RamiroMadera/Proyecto_GENERATOR/firmware_v3/documentation/CIAA_Boards/NXP_LPC54102/Pico-CIAA/Guia_picoCIAAv1.0_rfz.pdf

# picoCIAA v1.0

### Especificaciones técnicas y detalle de conectores

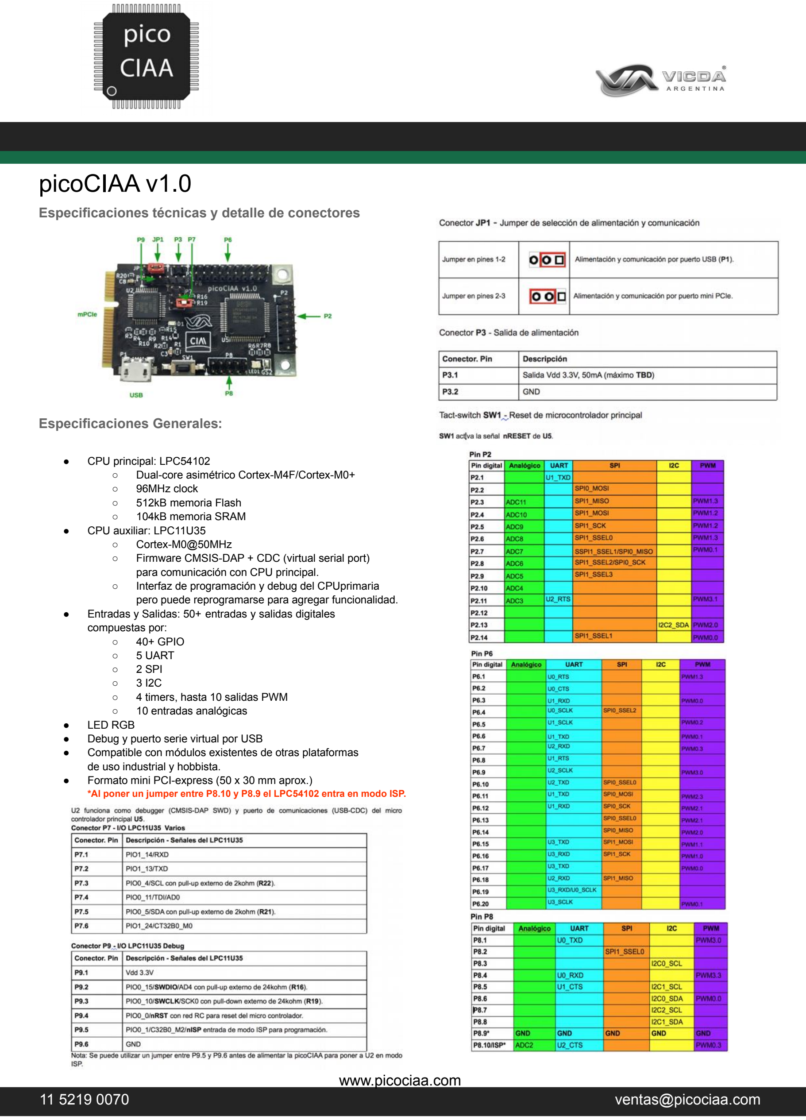
[picture p9: page 1]

### Especificaciones Generales:

- CPU principal: LPC54102
- Dual-core asimétrico Cortex-M4F/Cortex-M0+
- 96MHz clock
- 512kB memoria Flash
- 104kB memoria SRAM
- CPU auxiliar: LPC11U35
- Cortex-M0@50MHz
- Firmware CMSIS-DAP + CDC (virtual serial port) para comunicación con CPU principal.
- Interfaz de programación y debug del CPUprimaria pero puede reprogramarse para agregar funcionalidad.
- Entradas y Salidas: 50+ entradas y salidas digitales compuestas por:
- 40+ GPIO
- 5 UART
- 2 SPI
- 3 I2C
- 4 timers, hasta 10 salidas PWM
- 10 entradas analógicas
- LED RGB
- Debug y puerto serie virtual por USB
- Compatible con módulos existentes de otras plataformas
de uso industrial y hobbista.
- Formato mini PCI-express (50 x 30 mm aprox.)
*Al poner un jumper entre P8.10 y P8.9 el LPC54102 entra en modo ISP.

## www.picociaa.com

11 5219 0070 | ventas@picociaa.com
