RamiroMadera/Proyecto_GENERATOR/firmware_v3/examples/c/sapi/bluetooth/MIT App Inventor 2.pdf

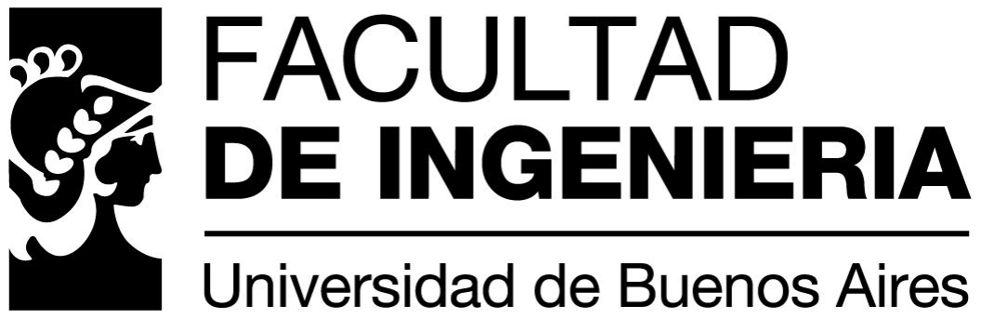
[picture p13: figure]

## Carrera de Especialización en Sistemas Embebidos (CESE) de la FI-UBA

### 8. Protocolos de comunicación en Sistemas Embebidos

MIT App Inventor 2

Profesores:
- Esp. Ing. Eric Pernia.
- Dr. Ing. Pablo Gómez.

“MIT App Inventor 2”
por Esp. Lic. Agustin Bassi, se distribuye bajo una Licencia Creative Commons Atribución-CompartirIgual 4.0 Internacional.

## Licencia

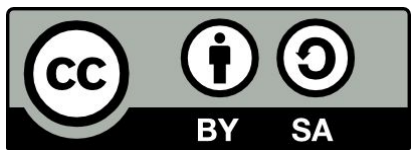
[picture p14: figure]

Para realizar una aplicación en Android para probar la comunicación con la EDU-CIAA-NXP vamos a utilizar APP Inventor, que es una herramienta sencilla para desarrollar aplicaciones Android evitando utilizar las herramientas típicas las cuales consisten en lenguaje de programación Java, XML, emulación virtual y el entorno de desarrollo Android Studio. (https://developer.android.com/studio/)

APP Inventor es un desarrollo de Google que permite programar aplicaciones para Android mediante programación gráfica. Posteriormente, el proyecto fue retomado por el MIT y ahora es conocido como MIT App Inventor 2.

MIT App Inventor 2 es una herramienta para desarrollo on line por lo que requiere conexión permanente a Internet.

## Introducción

Paso 1

Tener una cuenta en Gmail
En https://accounts.google.com/ se puede crear una cuenta. Si ya se tiene cuenta, este paso es innecesario.

Paso 2

Ir a la página de MIT App Inventor 2
Dirigirse a http://appinventor.mit.edu/explore/front.html Allí inicia todo!

## Configuración APP Inventor 2

Paso 3 - Iniciar MIT App Inventor

Dirigirse a http://appinventor.mit.edu/explore/index-2.html y dar clic en “Create Apps”.

## Configuración APP Inventor 2

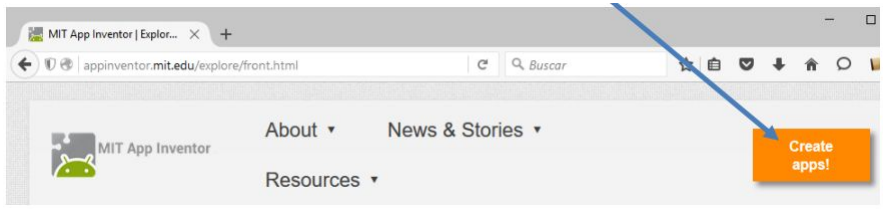
[picture p15: figure]

Paso 4 - Acceder a APP Inventor 2 con la cuenta de Google.

## Configuración APP Inventor 2

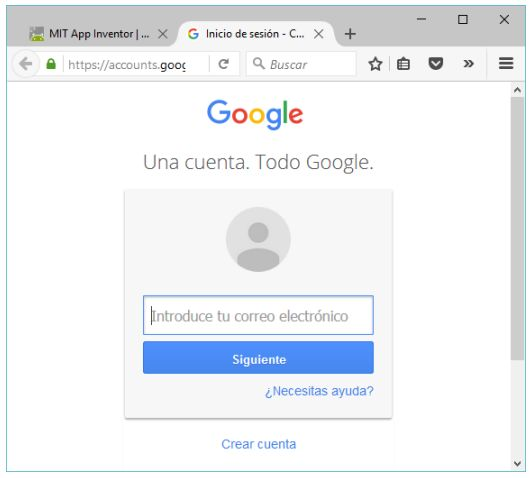
[picture p16: figure]

Paso 5 - Pantalla de inicio APP Inventor.

Al ser la primera vez, no se tienen proyectos en la cuenta.

## Configuración APP Inventor 2

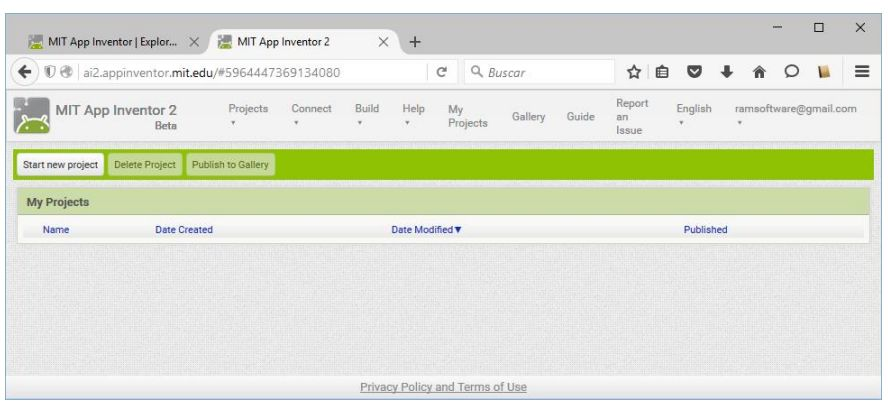
[picture p17: figure]

Paso 6 - Cambiar idioma en APP Inventor

Si es de preferencia, cambiar el idioma a Español.

## Configuración APP Inventor 2

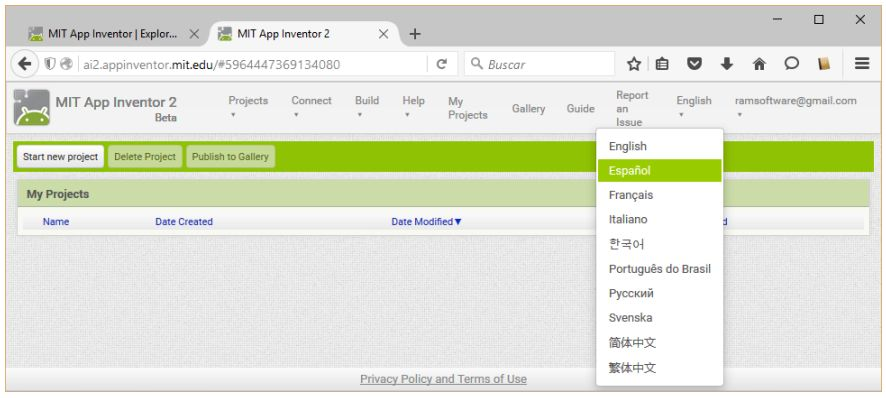
[picture p18: figure]

Paso 7 - Aceptar la información.
Tildar la opción “Do not show Again” para que no vuelva a aparecer este cartel nuevamente.

## Configuración APP Inventor 2

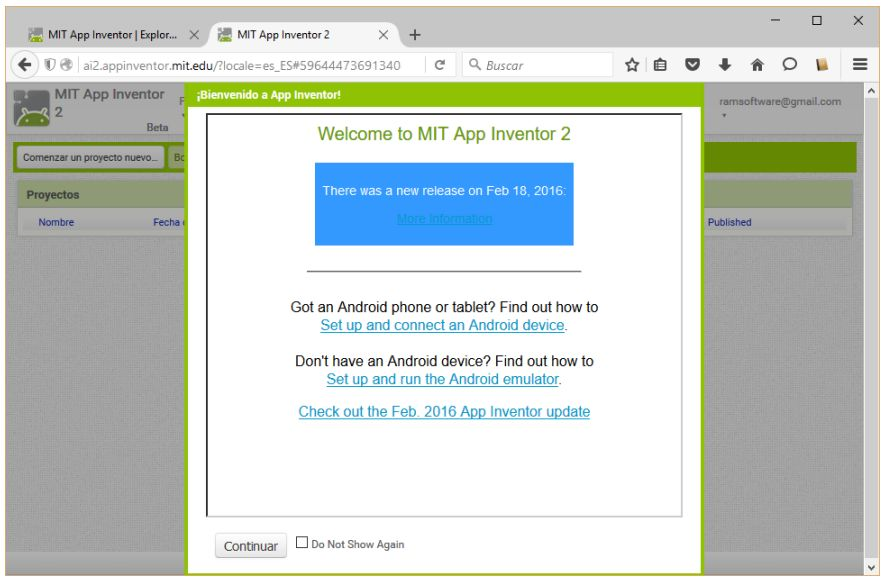
[picture p19: figure]

Paso 8 - Fin de la configuración

Bienvenido a APP Inventor 2 !!!

## Configuración APP Inventor 2

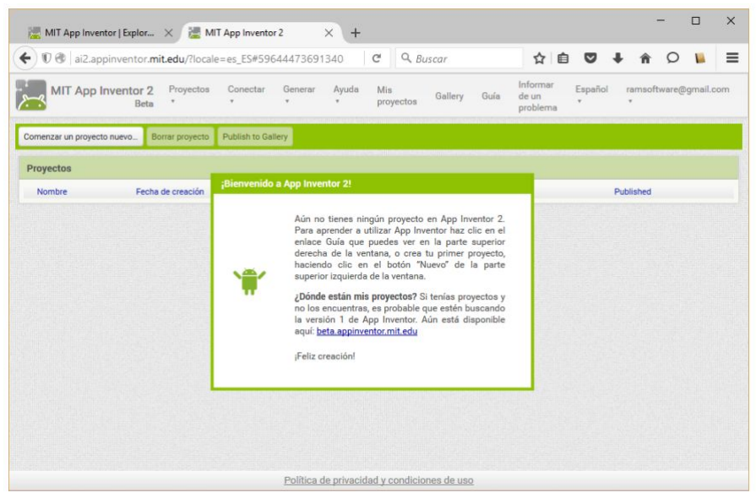
[picture p20: figure]

APP Inventor 2 permite debuggear la aplicación creada directamente en el celular.

Para que esto sea posible es necesario instalar una aplicación de APP Inventor 2 que se encuentra en el Play Store de Google.

Descargar la aplicación y dar los permisos necesarios para que pueda ejecutarse.

## Instalar aplicación APP Inventor 2

## Instalar aplicación APP Inventor 2

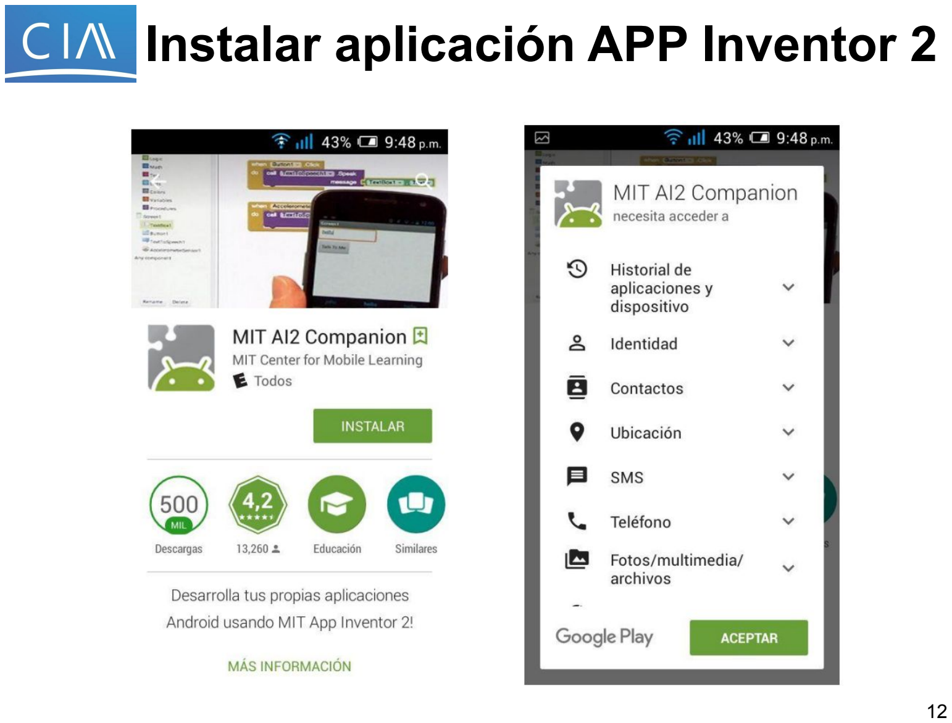
[picture p21: page 12]

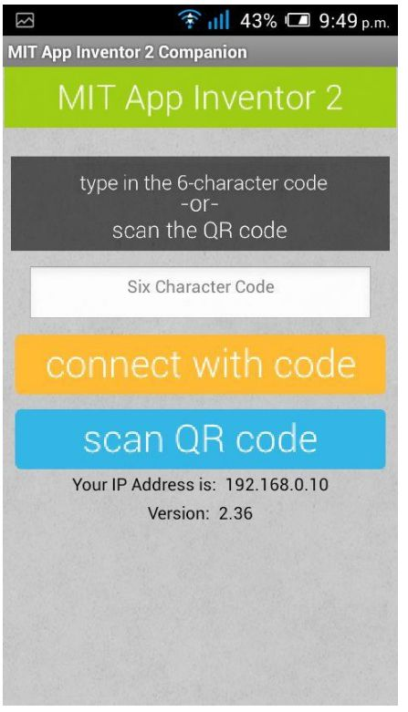
[picture p22: figure]

La aplicación MIT App
Inventor 2 Companion va a
permitir vincular el
desarrollo realizado dentro de la web con el
smartphone personal.

Mediante el escaneo de un
código QR o la escritura del código provisto en la web, automáticamente se carga
la aplicación desarrollada en el smartphone.

## Instalar aplicación APP Inventor 2

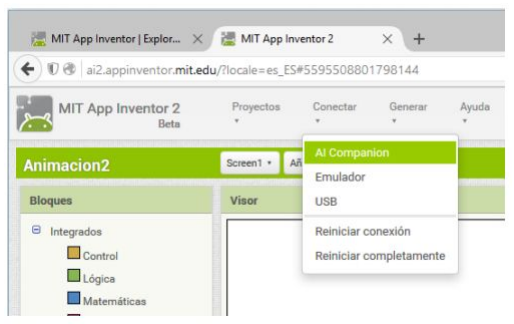
[picture p23: figure]

Dentro de la web de App
Inventor 2, seleccionar
“Conectar” y luego “AI
Companion”.

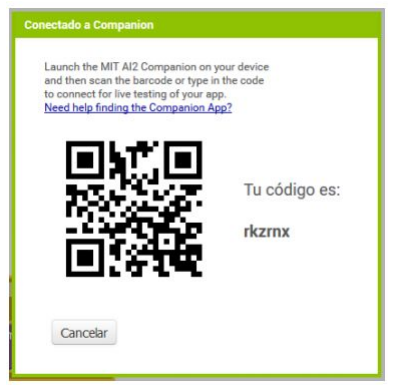
[picture p24: figure]

Esto genera el código QR
que debe ser escaneado
desde la aplicación de APP Inventor previamente
instalada en el smartphone.

## Instalar aplicación APP Inventor 2

# ¿Preguntas?

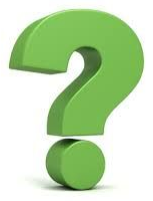
[picture p25: figure]

## Consultas:

ericpernia@gmail.com
elpablogomez@gmail.com
sergiordj@gmail.com

# ¡Muchas gracias!

- http://www.bolanosdj.com.ar/MOVIL/LENGUAJES/Usan

do-MIT-App-Inventor-2.pdf (http://www.bolanosdj.com.ar/MOVIL/LENGUAJES/Usando-MIT-App-Inventor-2.pdf)

- http://ai2.appinventor.mit.edu/

## Bibliografía
