RamiroMadera/Proyecto_GENERATOR/firmware_v3/examples/c/sapi/bluetooth/hc05_uart_bridge/APP Inventor - Hola Mundo con HC05 o HC06.pdf

# Carrera de Especialización en Sistemas Embebidos (CESE) de la FI-UBA

## 8. Protocolos de comunicación en Sistemas Embebidos

## APP Inventor - Hola Mundo con HC05 o HC06

Profesores:
- Esp. Ing. Eric Pernia.
- Dr. Ing. Pablo Gómez.

## “APP Inventor - Hola Mundo!” por Esp. Lic. Agustin Bassi, se distribuye bajo una Licencia Creative Commons Atribución-CompartirIgual 4.0

Internacional.

# Licencia


## El objetivo será crear una aplicación Android que tenga comunicación con la EDU-CIAA-NXP mediante el módulo

Bluetooth HC05 o HM10.

Los materiales necesarios serán.

- EDU-CIAA-NXP.
- Módulo HC05 o HM10.
- Cables de conexión entre EDU CIAA y HC05.
- Cuenta creada en APP Inventor.
- Smartphone con Android.

# Introducción

# Cargar programa en EDU CIAA

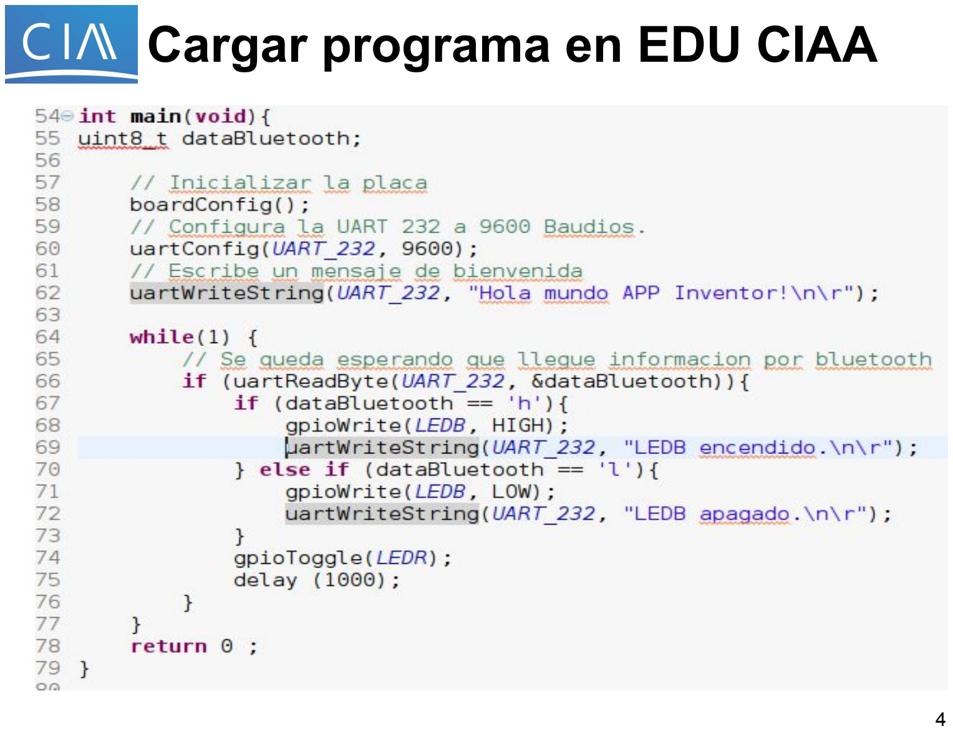
[picture p26: page 4]

## Comenzar creando un proyecto nuevo con el botón “Comenzar

nuevo proyecto”.

Ingresar como nombre Estación Metereológica.

# Hola Mundo App Inventor 2!

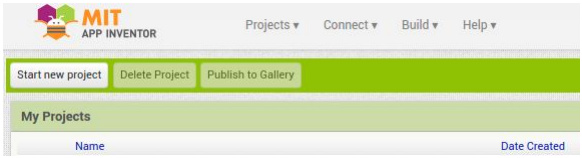
[picture p27: figure]

Al iniciar el proyecto, se verá una ventana como esta.

# Hola Mundo App Inventor 2!

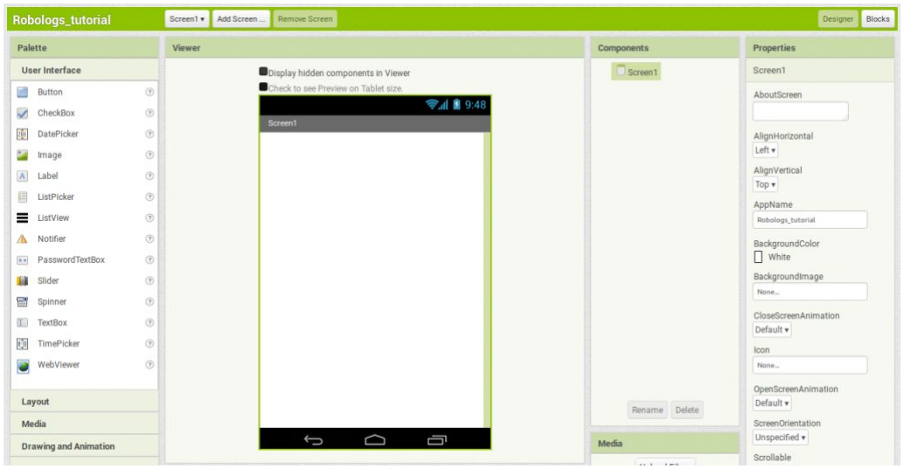
[picture p28: figure]

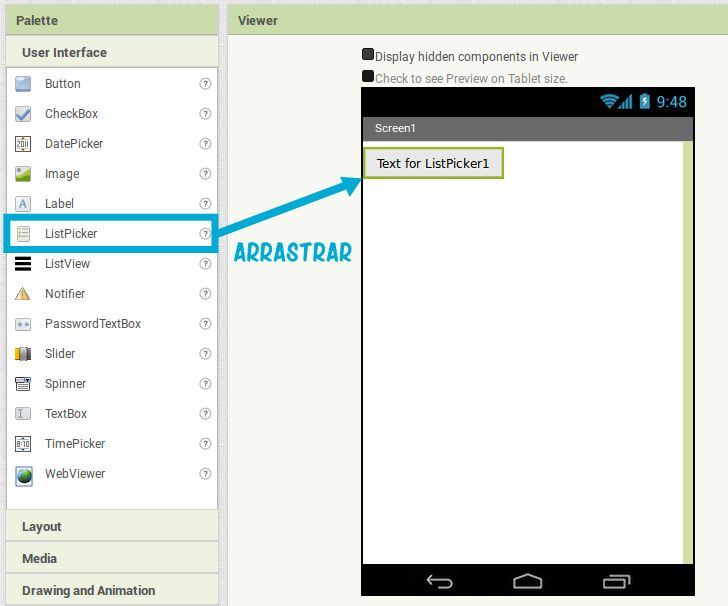
[picture p29: figure]

Empezar yendo a

Palette y buscar el

elemento List Picker.

Se trata de menú

desplegable, que se

programa para que

muestre los

dispositivos Bluetooth

cercanos y se conecte

a uno. Arrastrarlo

hasta la pantalla.

# Hola Mundo App Inventor 2!

A la derecha, en el menú Properties, cambiar el texto

del List Picker. Escribir “Dispositivos”.

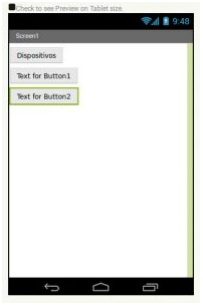
[picture p30: figure]

Volver al menú Palette y añadir dos elementos de tipo

Button a la aplicación, de la misma forma que se

colocó el List Picker.

Seleccionar cada uno de los botones y cambiarles el

nombre. A uno llamar “Encender LED” y al otro

“Apagar LED”. Con un botón se encenderá el LEDB y

con el otro se apagará.

# Hola Mundo App Inventor 2!

La comunicación entre la APP y el sistema embebido debe ser

bidireccional. Se deben agregar los objetos destinados a la

recepción de datos.

Agregar desde el menú | Palette->User Interface | un objeto del tipo

Label y en sus propiedades escribirle el texto “Información

Recibida”.

Como último objeto visual, debajo del Label agregar un TextBox.

# Hola Mundo App Inventor 2!

Lo que se ha añadido hasta ahora son componentes visibles. El usuario puede verlos e interactuar con ellos. Pero hay otro tipo de componentes, llamados non-visible components, que sirven para activar algunas funcionalidades como el Giroscopio, la antena WiFi o Bluetooth.

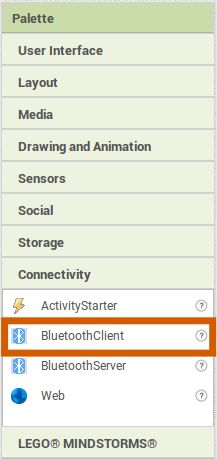
[picture p31: figure]

Para poder conectar con la CIAA se necesita que la aplicación pueda usar la antena Bluetooth.

Ir a Palette->Connectivity y arrastrar Bluetooth Client a la pantalla.

# Hola Mundo App Inventor 2!

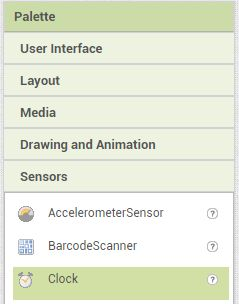
[picture p32: figure]

El último objeto necesario a agregar es

un timer que chequee si hay información

disponible proveniente del sistema

embebido.

Esto se realiza desde | Palette->Sensors
y arrastrando un objeto | Clock.

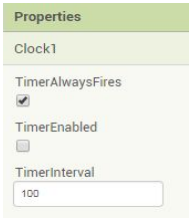
[picture p33: figure]

En las propiedades del clock setear que

se dispare cada 100 ms y que arranque

deshabilitado.

# Hola Mundo App Inventor 2!

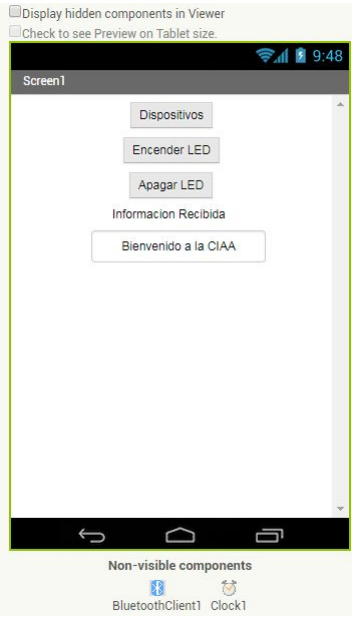
[picture p34: figure]

A esta altura, la aplicación debería lucir como en la imagen.

Hasta aquí el diseño. Es hora de configurar cada uno de los componentes.

Arriba a la derecha hay dos botones juntos: Design y Blocks. El primero abre la ventana de diseño, que permite colocar todos los
componentes de la aplicación. Blocks abre una ventana para programar los bloques.

# Hola Mundo App Inventor 2!

Lo primero es programar el menú desplegable. A la derecha, seleccionar ListPicker1 y se abrirá un menú en el que aparecen los bloques relacionados con este objeto.
Hay que programar en el desplegable dos cosas: qué debe hacer ANTES de seleccionar una opción del menú desplegable y DESPUÉS de seleccionar una.

Antes de seleccionar una opción,

inicializar una lista con los nombres

de todos los dispositivos Bluetooth

que hay cerca.

Si el móvil tiene la comunicación

Bluetooth activada, ListPicker1

deberá establecer los nombres de

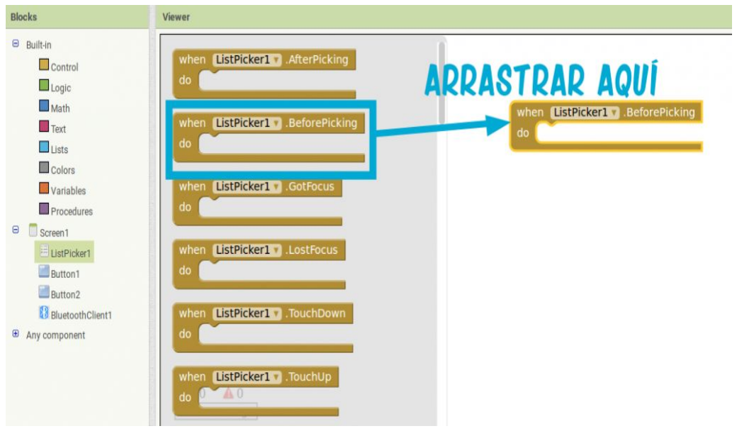
[picture p35: figure]

los dispositivos cercanos como elementos de la lista.

Dentro del menú de bloques de | ListPicker1 arrastrar. BeforePicking | al espacio
en blanco.

# Hola Mundo App Inventor 2!

# Hola Mundo App Inventor 2!

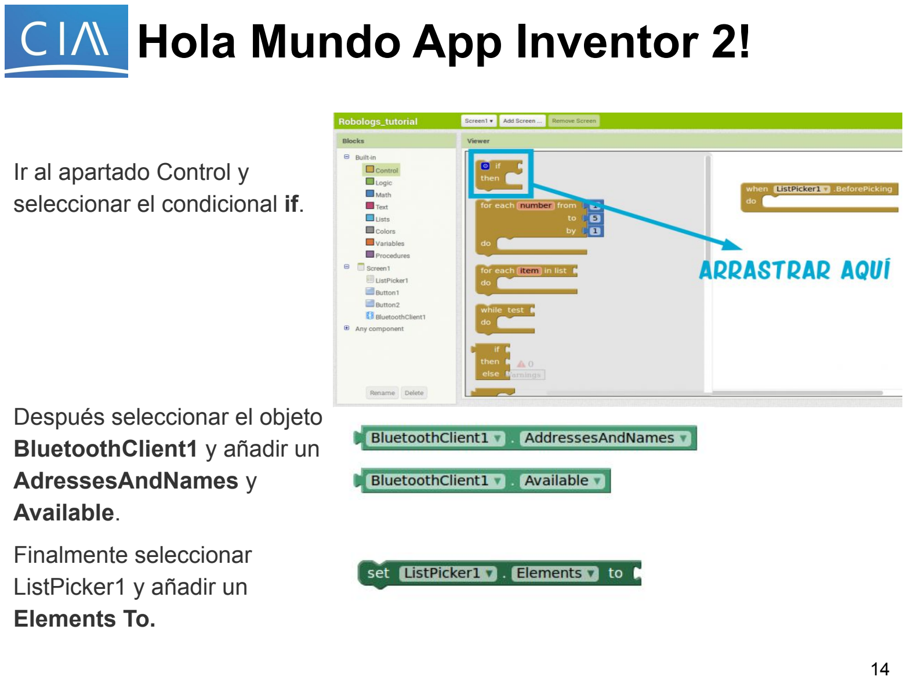
[picture p36: page 14]

Ir al apartado Control y
seleccionar el condicional if.

Después seleccionar el objeto
BluetoothClient1 | y añadir un
AdressesAndNames | y
Available.

Finalmente seleccionar
ListPicker1 y añadir un
Elements To.

# Hola Mundo App Inventor 2!

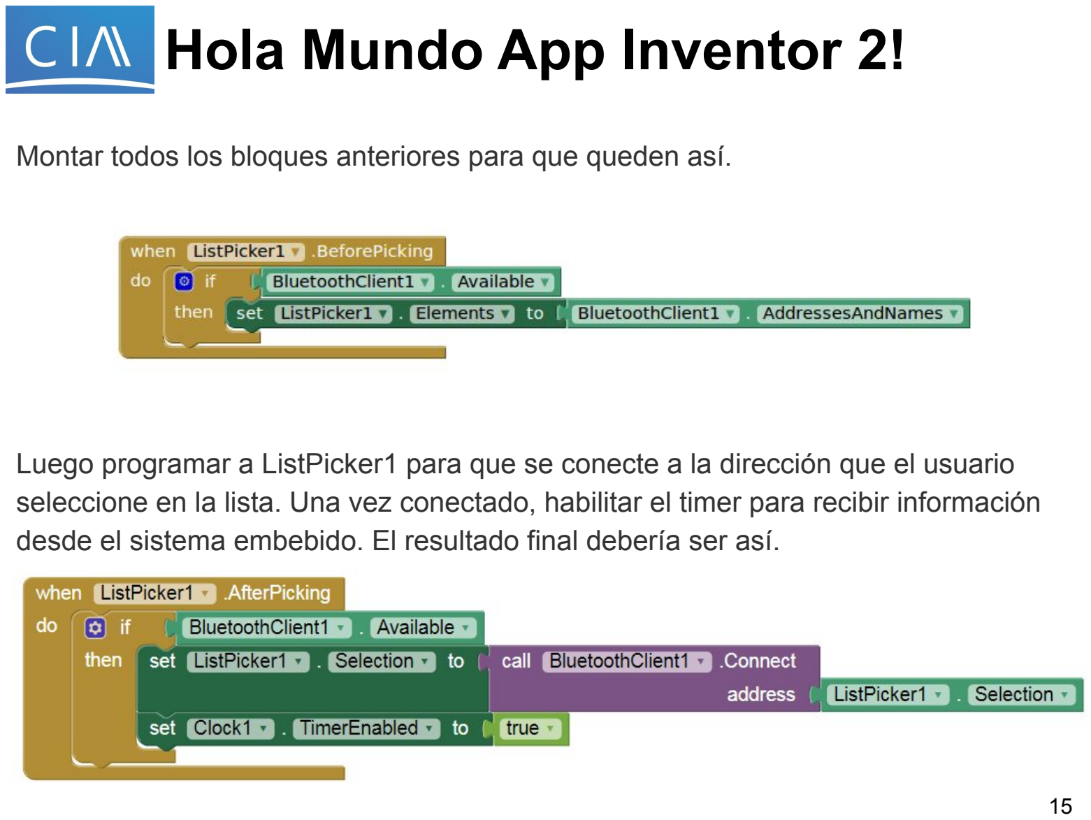
[picture p37: page 15]

Montar todos los bloques anteriores para que queden así.

Luego programar a ListPicker1 para que se conecte a la dirección que el usuario seleccione en la lista. Una vez conectado, habilitar el timer para recibir información desde el sistema embebido. El resultado final debería ser así.

Al inicio de la aplicación deshabilitar el campo de texto donde se va a mostrar la info recibida así no se puede escribir en ese campo.

Si la aplicación recibe un dato enviado desde el sistema embebido lo debe mostrar en el campo de texto. Para chequear si la aplicación recibió datos, es necesario chequear periódicamente mediante el timer si hay datos disponibles en el objeto de conexión BluetoothClient1

# Hola Mundo App Inventor 2!

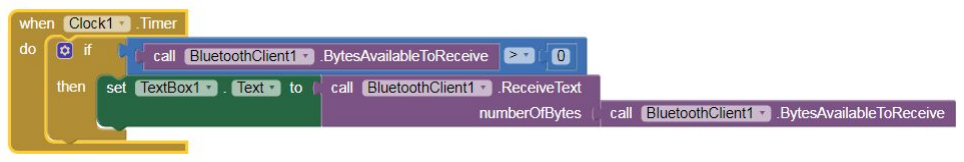
[picture p38: figure]

Finalmente configurar Button1 y Button2 para que al pulsarlos se envíe un texto a la dirección Bluetooth conectado.

# Hola Mundo App Inventor 2!

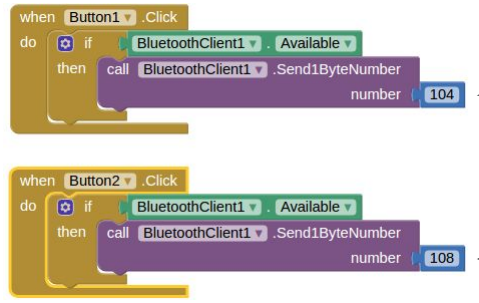
[picture p39: figure]

Corresponde al
ASCII ‘h’

Corresponde al
ASCII ‘l’

# Hola Mundo App Inventor 2!

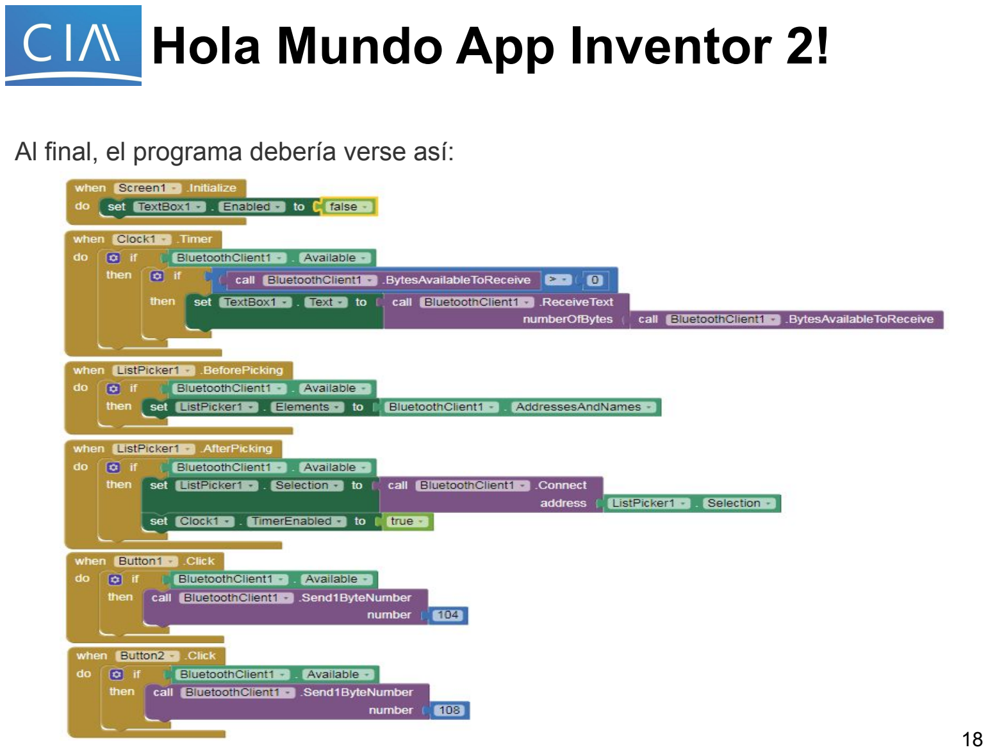
[picture p40: page 18]

Al final, el programa debería verse así:

# Hola Mundo App Inventor 2!

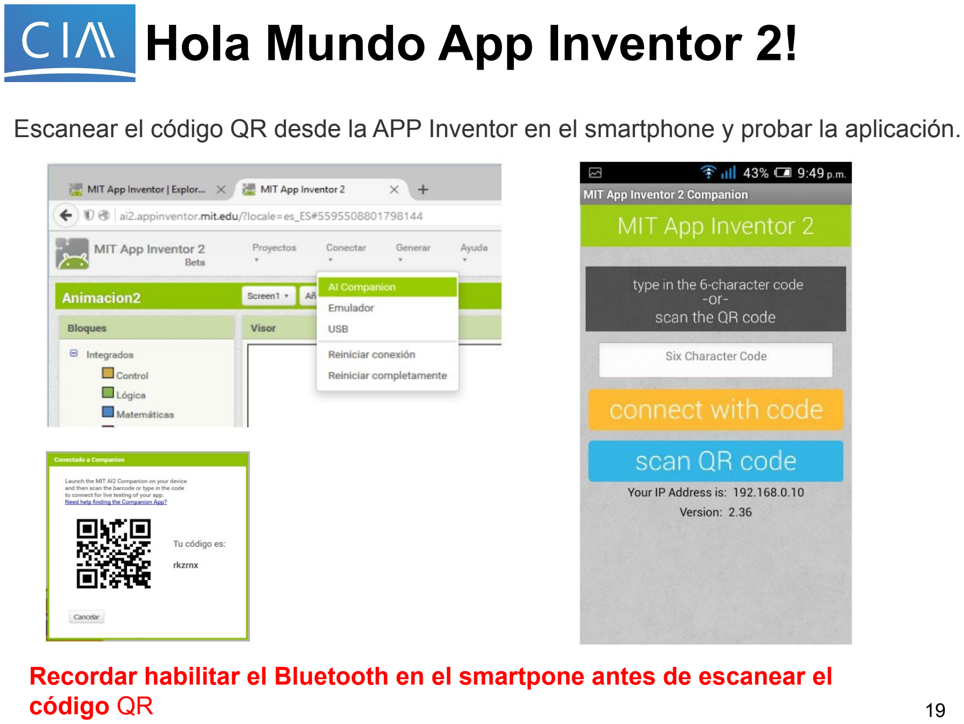
[picture p41: page 19]

Escanear el código QR desde la APP Inventor en el smartphone y probar la aplicación.

Recordar habilitar el Bluetooth en el smartpone antes de escanear el código QR

# ¿Preguntas?


# Consultas:

## ericpernia@gmail.com elpablogomez@gmail.com sergiordj@gmail.com

# ¡Muchas gracias!

## - http://ai2.appinventor.mit.edu/

## - http://www.bolanosdj.com.ar/MOVIL/LENGUAJES/Usan

do-MIT-App-Inventor-2.pdf (http://www.bolanosdj.com.ar/MOVIL/LENGUAJES/Usando-MIT-App-Inventor-2.pdf)

## - http://codeweek.eu/resources/spain/guia-iniciacion-app-

## inventor.pdf (http://codeweek.eu/resources/spain/guia-iniciacion-app-inventor.pdf)

## - https://robologs.net/2015/10/29/tutorial-de-arduino-bluet

ooth-y-android-2-crear-una-app-con-mit-inventor/ (https://robologs.net/2015/10/29/tutorial-de-arduino-bluetooth-y-android-2-crear-una-app-con-mit-inventor/)

# Bibliografía
