RamiroMadera/Proyecto_GENERATOR/firmware_v3/documentation/firmware/eclipse/Eclipse-Win01.png

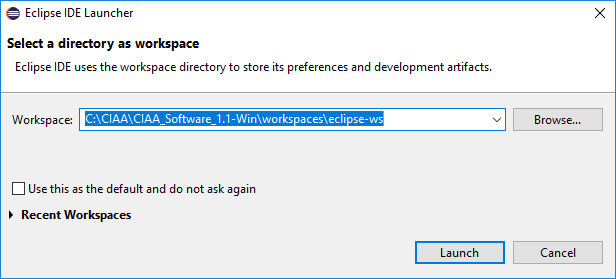
firmware_v3/documentation/firmware/eclipse/Eclipse-Win01.png
