RamiroMadera/Proyecto_GENERATOR/firmware_v3/documentation/firmware/eclipse/Eclipse-Win08.png

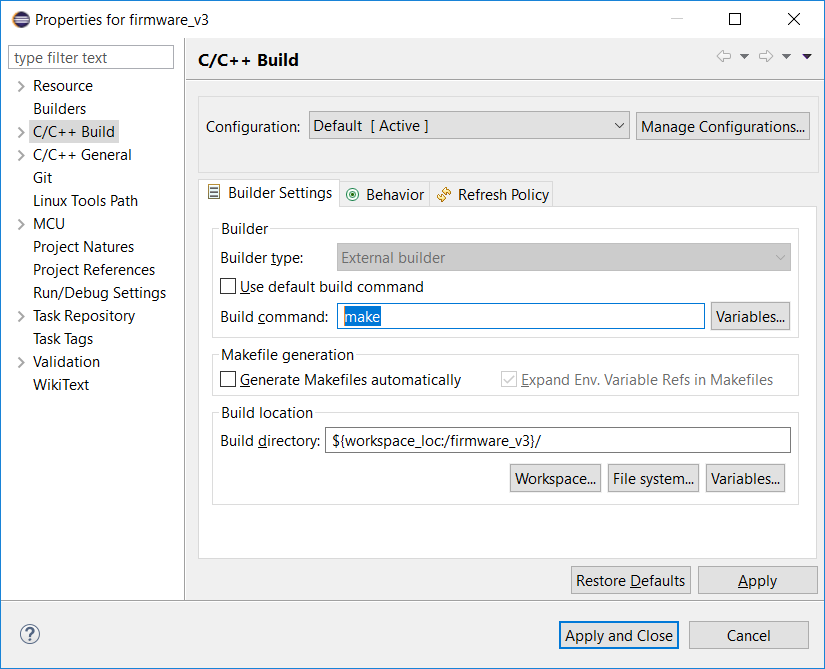
firmware_v3/documentation/firmware/eclipse/Eclipse-Win08.png
