RamiroMadera/Proyecto_GENERATOR/firmware_v3/documentation/firmware/eclipse/targets-03.png

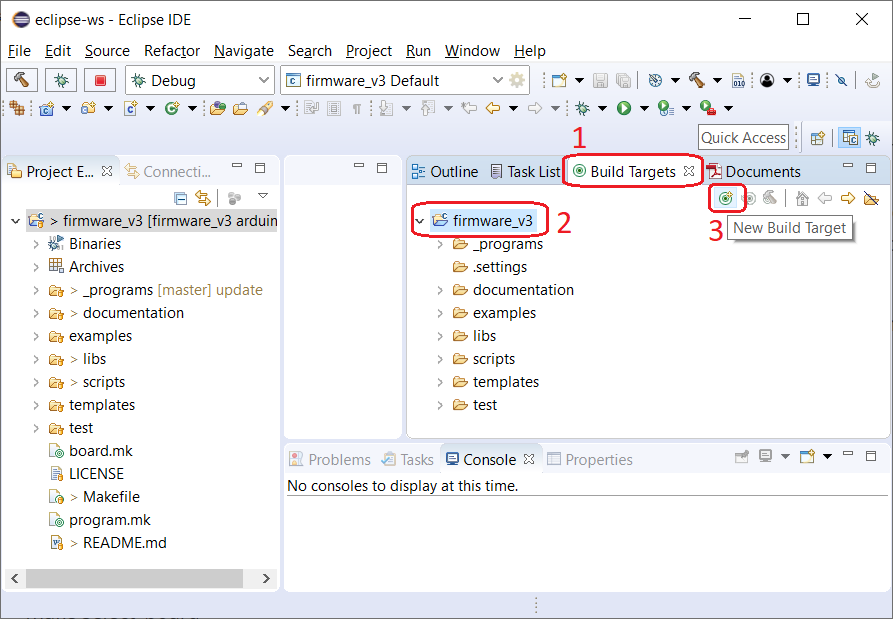
firmware_v3/documentation/firmware/eclipse/targets-03.png
