RamiroMadera/Proyecto_GENERATOR/firmware_v3/documentation/firmware/eclipse/targets-05.png

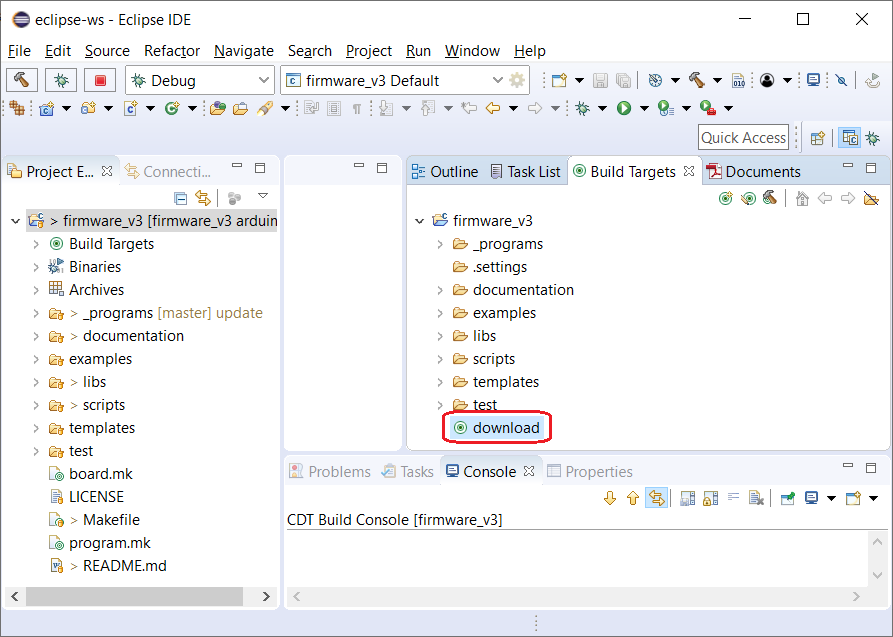
firmware_v3/documentation/firmware/eclipse/targets-05.png
