RamiroMadera/Proyecto_GENERATOR/firmware_v3/documentation/firmware/embedded_ide/open01.png

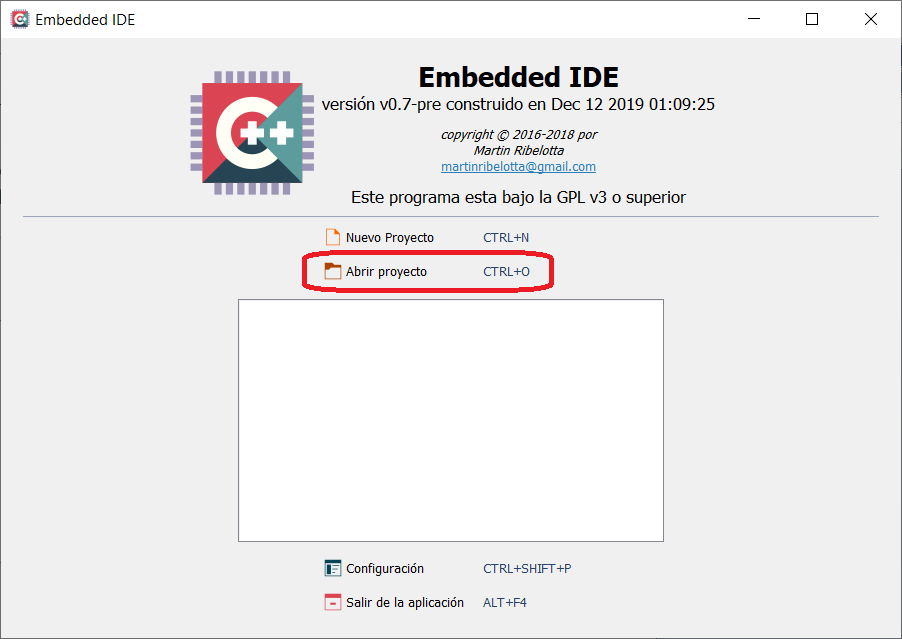
firmware_v3/documentation/firmware/embedded_ide/open01.png
