RamiroMadera/Proyecto_GENERATOR/firmware_v3/documentation/firmware/embedded_ide/open03.png

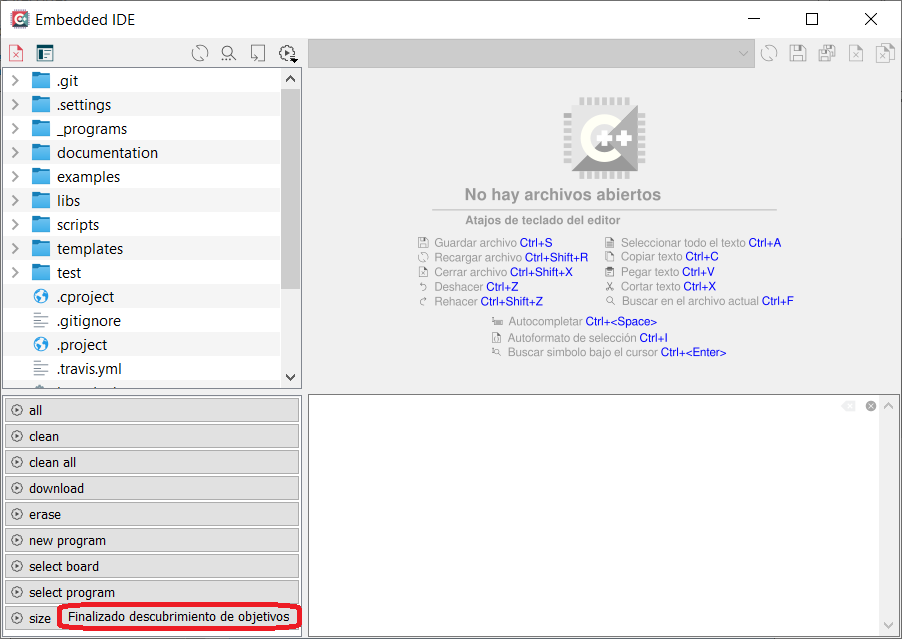
firmware_v3/documentation/firmware/embedded_ide/open03.png
