RamiroMadera/Proyecto_GENERATOR/firmware_v3/documentation/firmware/embedded_ide/targets.png

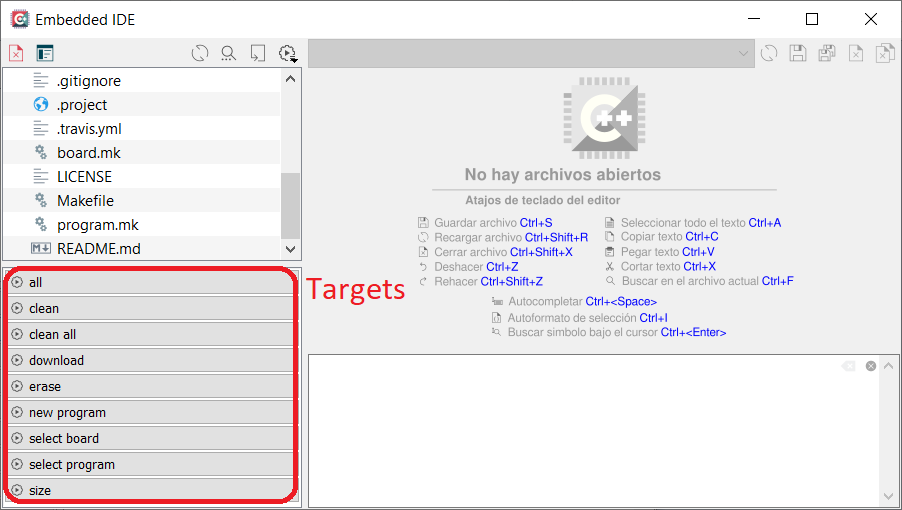
firmware_v3/documentation/firmware/embedded_ide/targets.png
