RamiroMadera/Proyecto_GENERATOR/firmware_v3/examples/c/lpc_open/timer_250ms_pulse/250msSignal.png

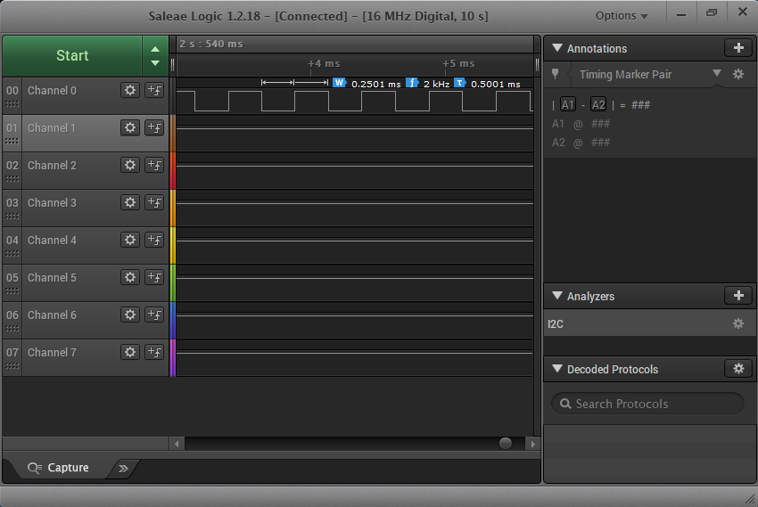
firmware_v3/examples/c/lpc_open/timer_250ms_pulse/250msSignal.png
