RamiroMadera/Proyecto_GENERATOR/firmware_v3/examples/c/sapi/adc_dac/adc_analog_stick_connection.png

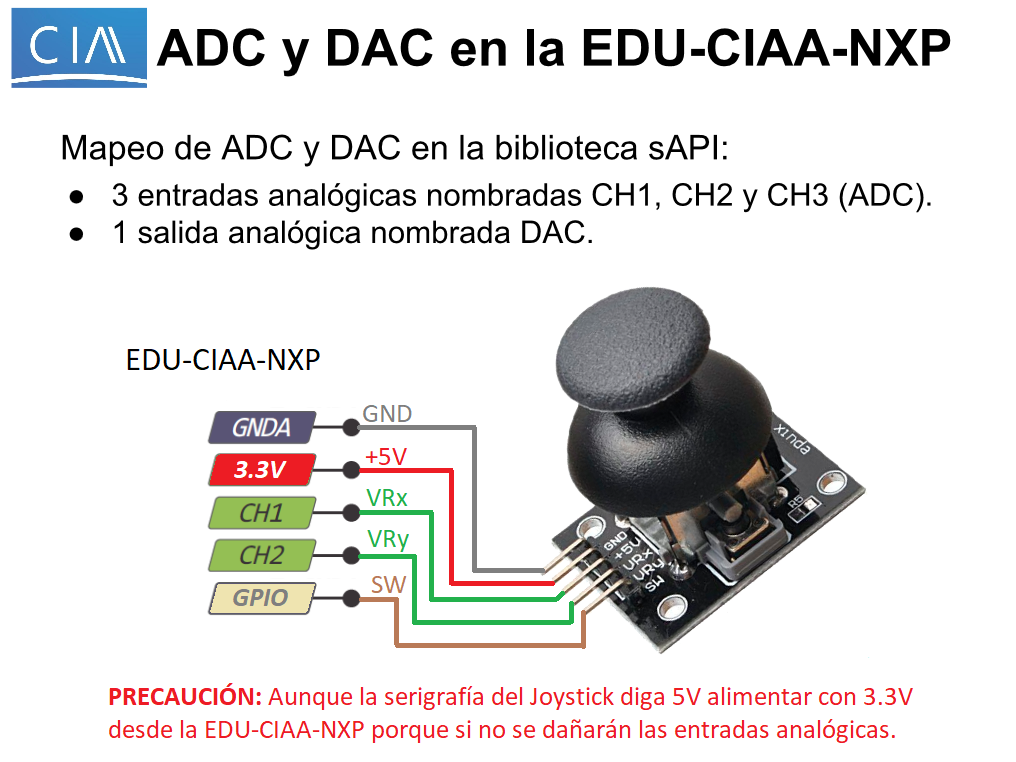
firmware_v3/examples/c/sapi/adc_dac/adc_analog_stick_connection.png
