RamiroMadera/Proyecto_GENERATOR/firmware_v3/examples/c/sapi/adc_dac/adc_dac_pins.png

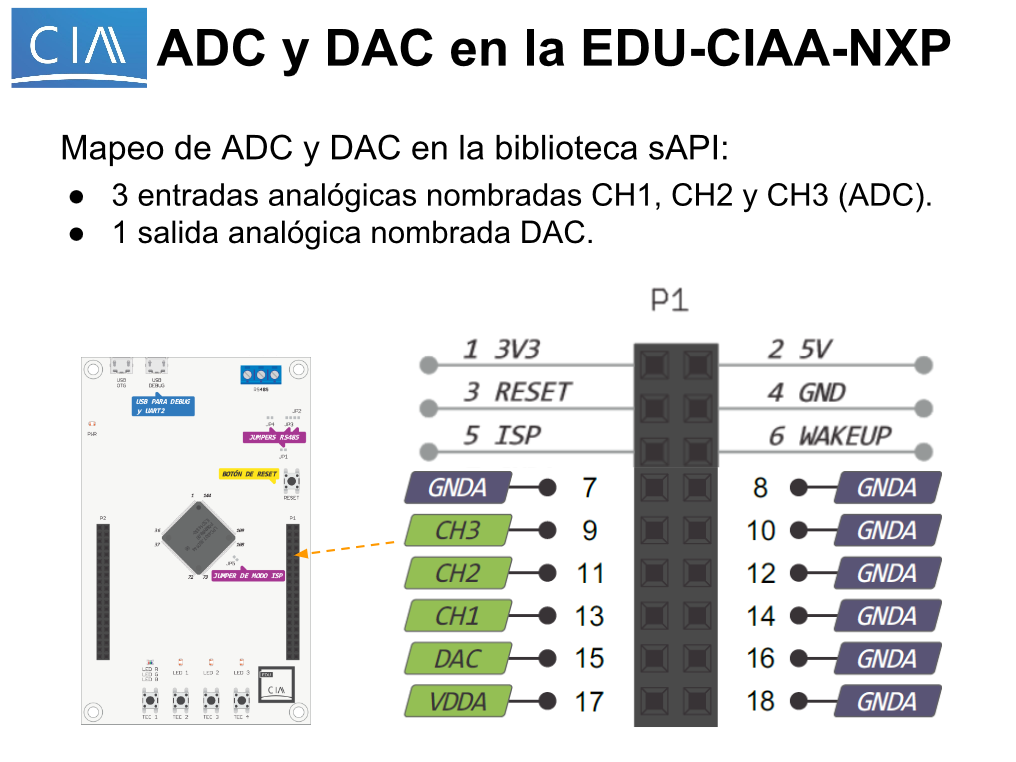
firmware_v3/examples/c/sapi/adc_dac/adc_dac_pins.png
