RamiroMadera/Proyecto_GENERATOR/firmware_v3/examples/c/sapi/bluetooth/hc05_uart_bridge/bluetooth_hc05_connection.png

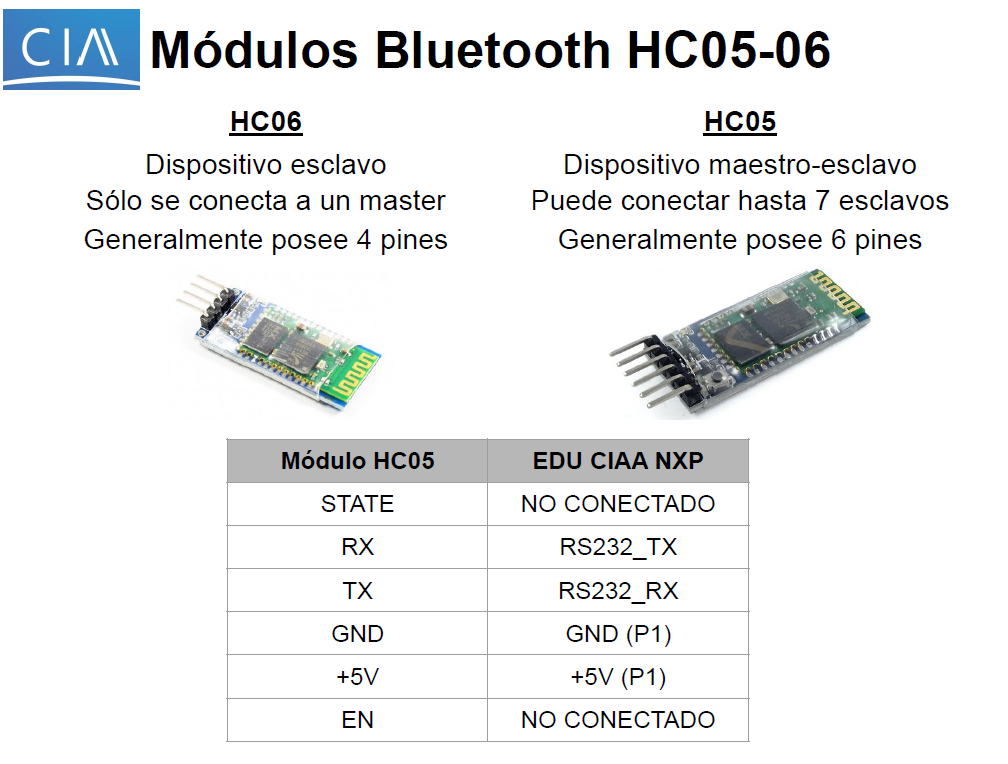
firmware_v3/examples/c/sapi/bluetooth/hc05_uart_bridge/bluetooth_hc05_connection.png
