RamiroMadera/Proyecto_GENERATOR/firmware_v3/examples/c/sapi/bluetooth/hm10_uart_bridge/bluetooth_ble_hm10_connection.png

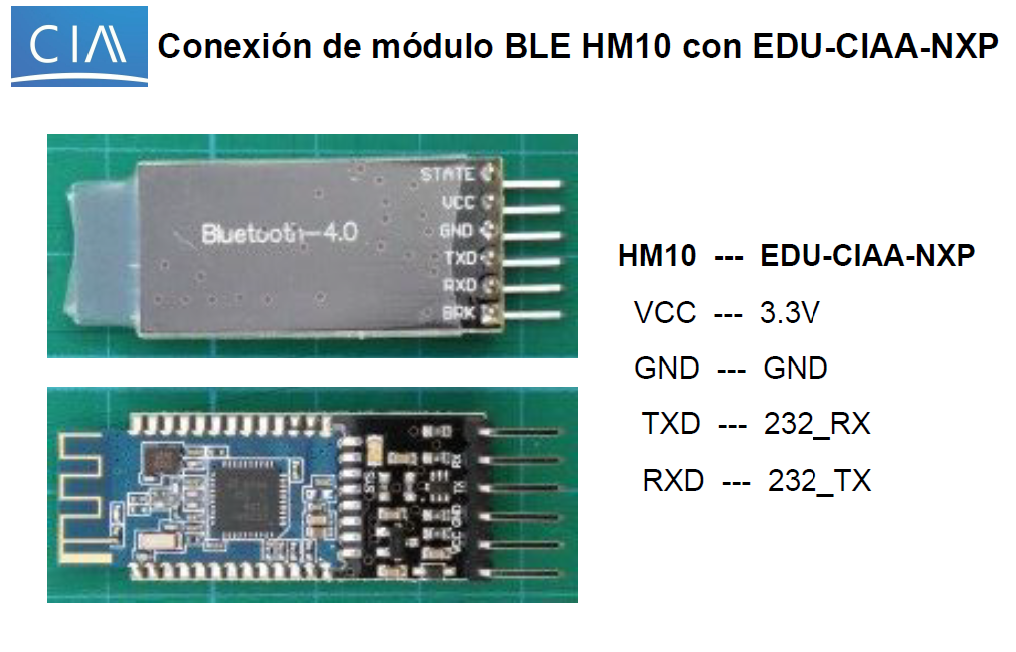
firmware_v3/examples/c/sapi/bluetooth/hm10_uart_bridge/bluetooth_ble_hm10_connection.png
