RamiroMadera/Proyecto_GENERATOR/firmware_v3/examples/c/sapi/dht11_temp_humidity/DHT11 Module and EDU-CIAA-NXP.png

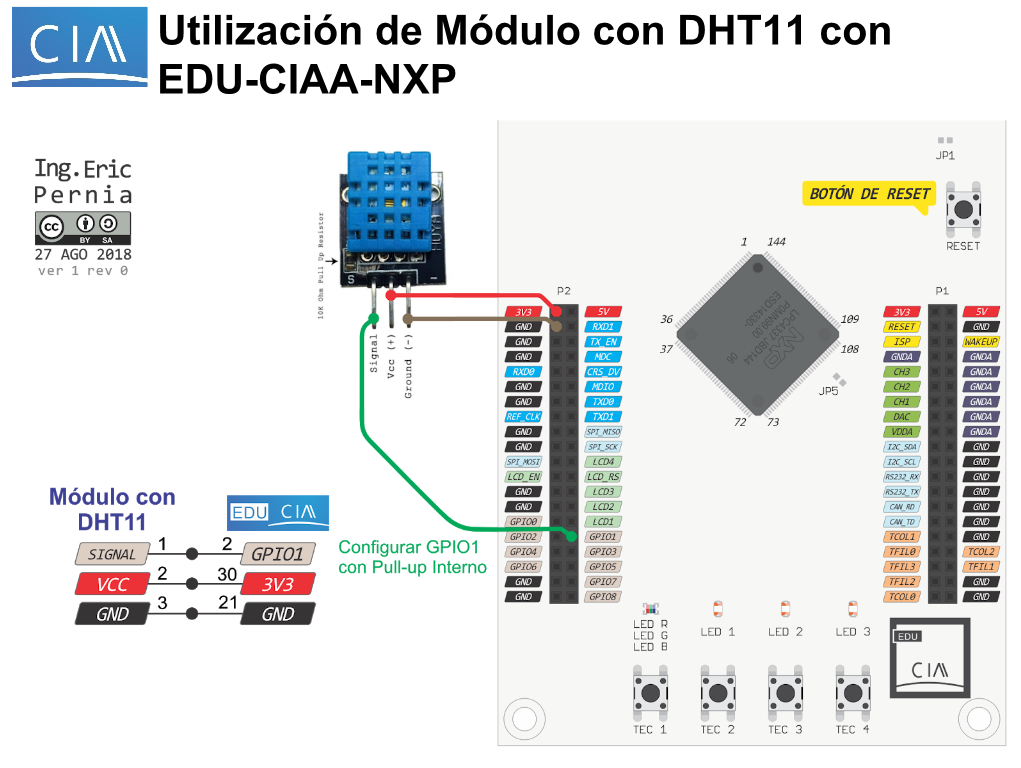
firmware_v3/examples/c/sapi/dht11_temp_humidity/DHT11 Module and EDU-CIAA-NXP.png
