RamiroMadera/Proyecto_GENERATOR/firmware_v3/examples/c/sapi/fatfs_sdcard_usbmsd/SD SPI.png

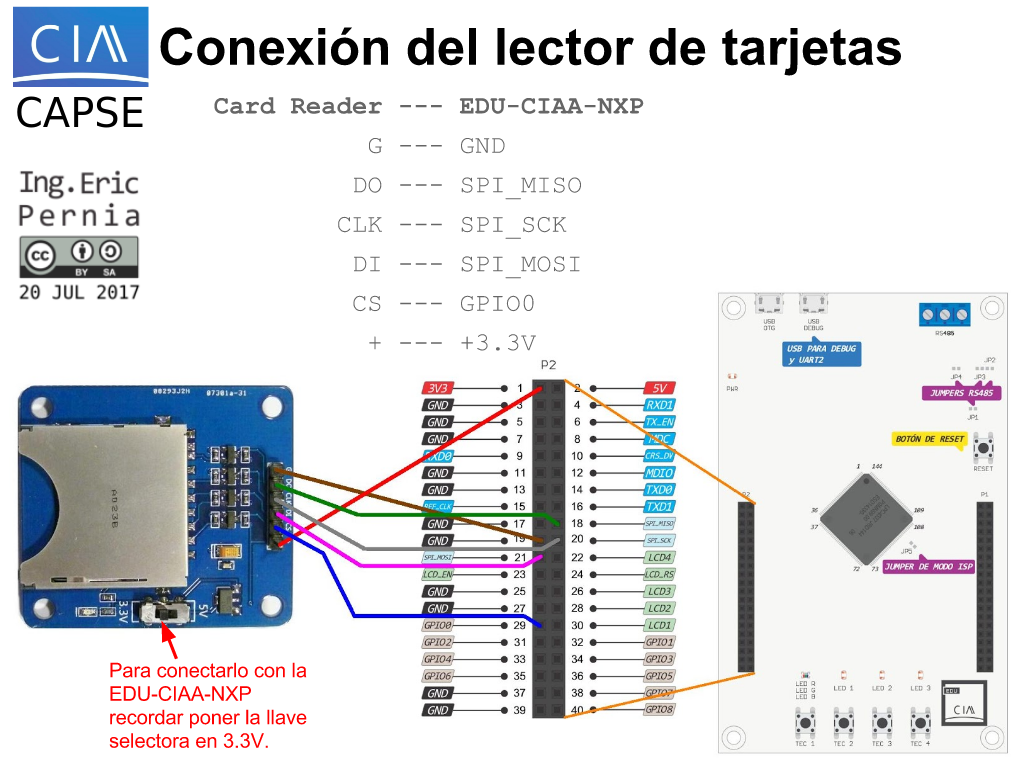
firmware_v3/examples/c/sapi/fatfs_sdcard_usbmsd/SD SPI.png
