RamiroMadera/Proyecto_GENERATOR/firmware_v3/examples/c/sapi/gpio/axis_interface/axis_pins_edu_ciaa.png

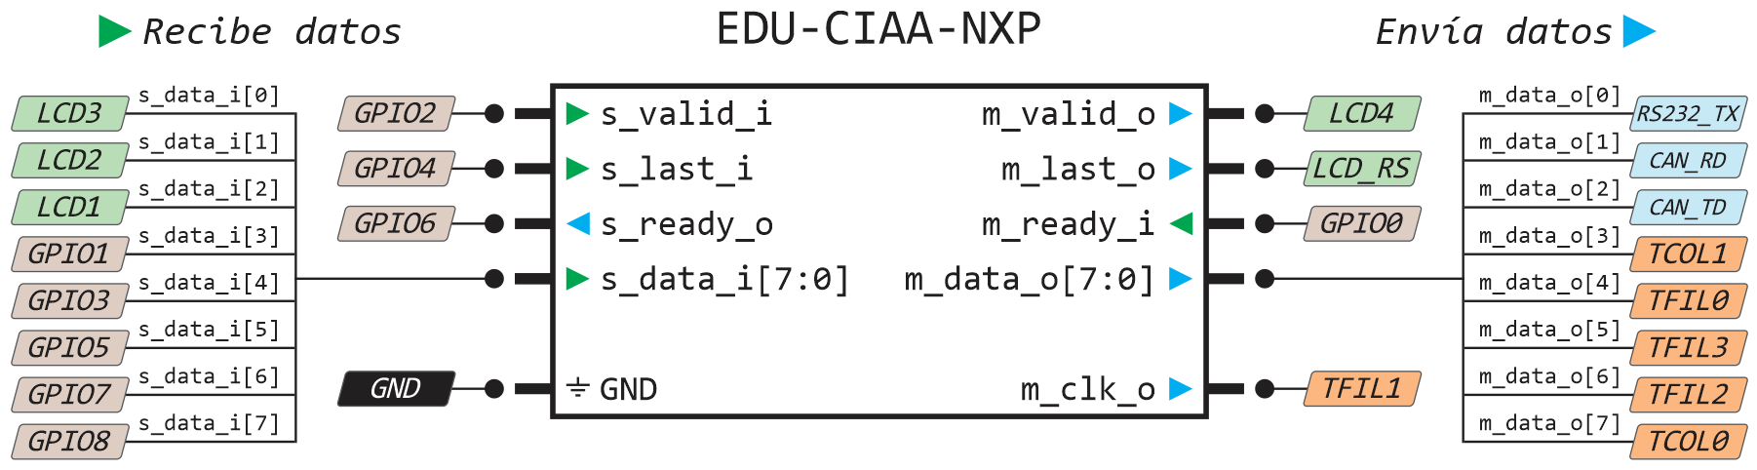
firmware_v3/examples/c/sapi/gpio/axis_interface/axis_pins_edu_ciaa.png
