RamiroMadera/Proyecto_GENERATOR/firmware_v3/examples/c/sapi/hcsr04_ultrasonic_sensor/Conexión EDU-CIAA - HC-SR04.png

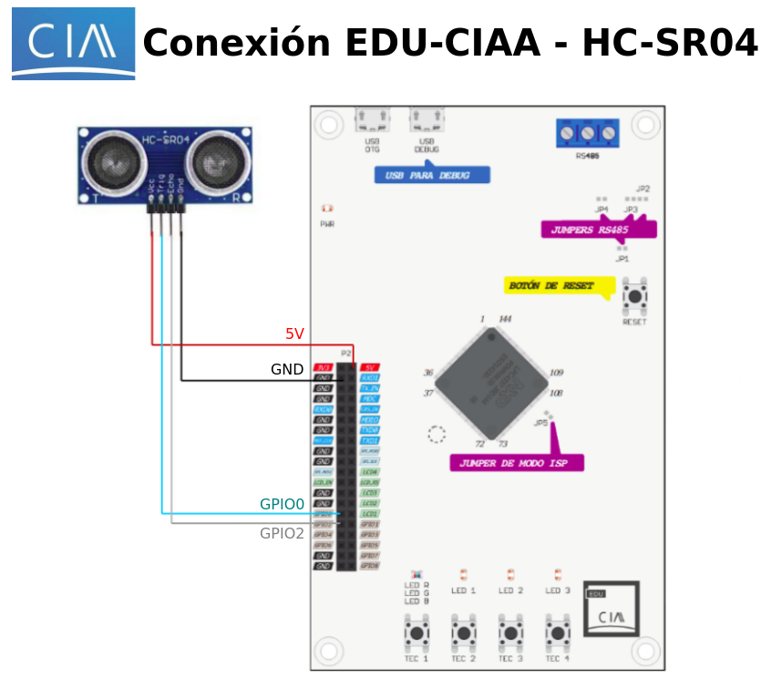
firmware_v3/examples/c/sapi/hcsr04_ultrasonic_sensor/Conexión EDU-CIAA - HC-SR04.png
