RamiroMadera/Proyecto_GENERATOR/firmware_v3/examples/c/sapi/i2c/IMUs/mpu9250/MPU9250 and EDU-CIAA-NXP.png

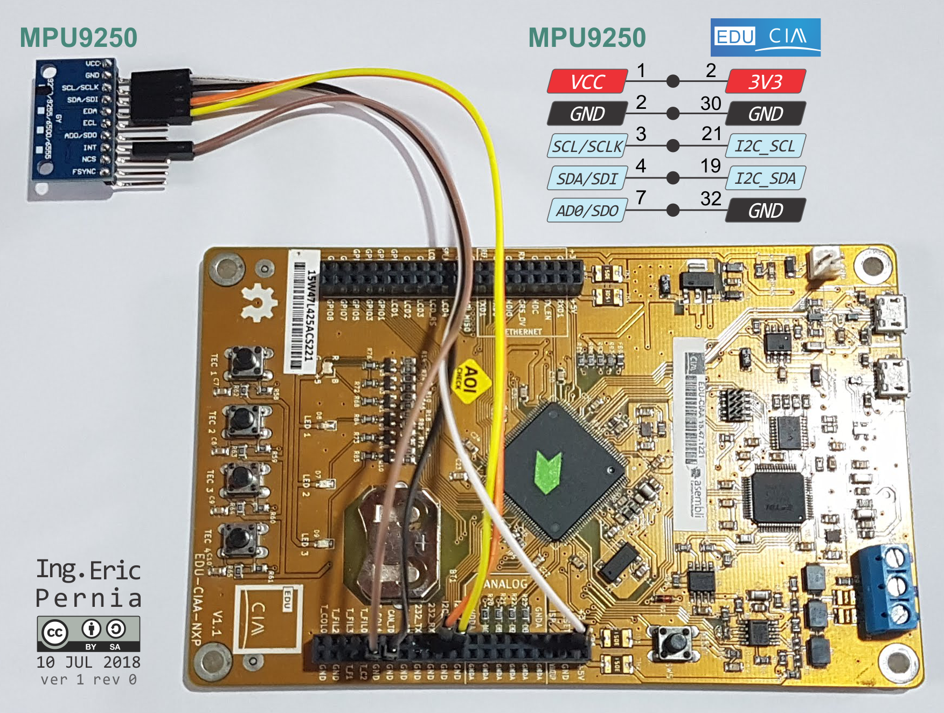
firmware_v3/examples/c/sapi/i2c/IMUs/mpu9250/MPU9250 and EDU-CIAA-NXP.png
