RamiroMadera/Proyecto_GENERATOR/firmware_v3/examples/c/sapi/i2c/IMUs/mpu9250/Serial Terminal - MPU9250 working.PNG

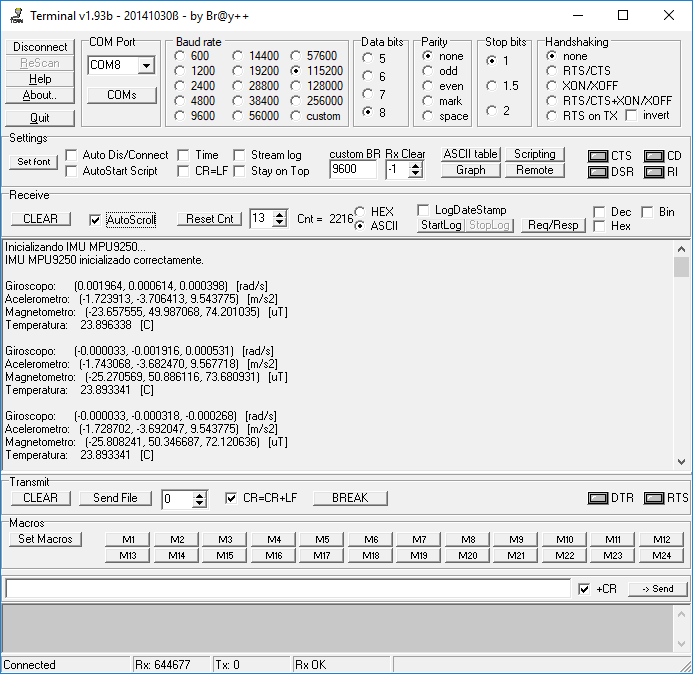
firmware_v3/examples/c/sapi/i2c/IMUs/mpu9250/Serial Terminal - MPU9250 working.PNG
