RamiroMadera/Proyecto_GENERATOR/firmware_v3/examples/c/sapi/i2c/magnetometers/hmc5883l/HMC5883L_EDU-CIAA.png

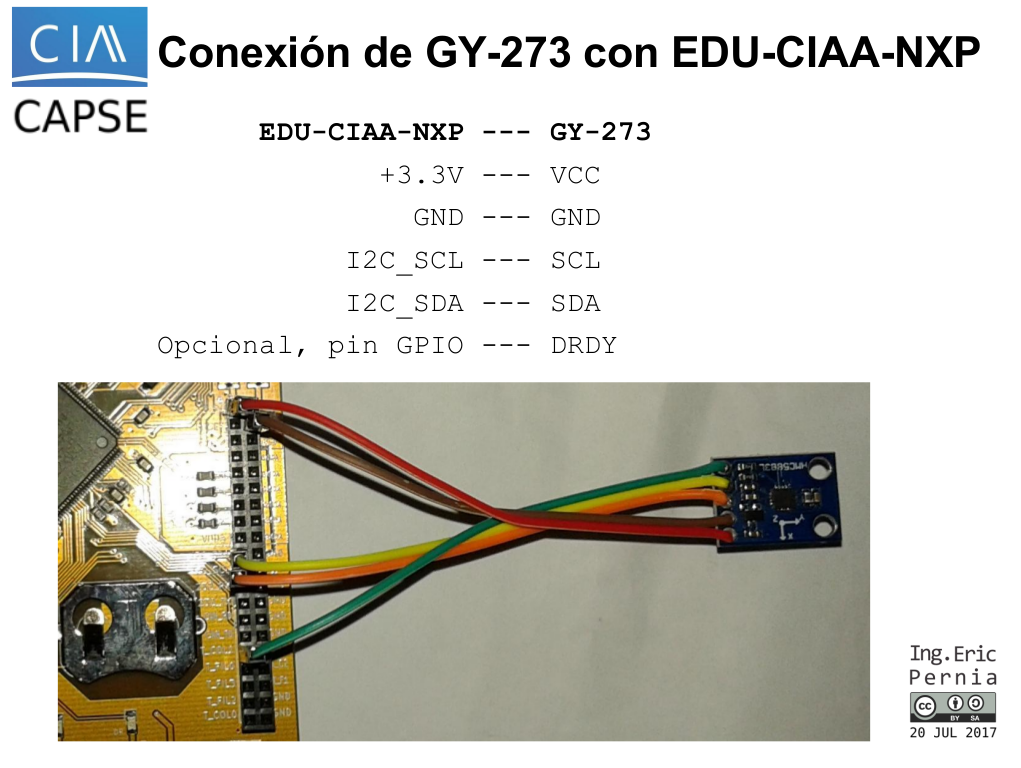
firmware_v3/examples/c/sapi/i2c/magnetometers/hmc5883l/HMC5883L_EDU-CIAA.png
