RamiroMadera/Proyecto_GENERATOR/firmware_v3/examples/c/sapi/keypad_7segment/7 segment display - EDU-CIAA-NXP.png

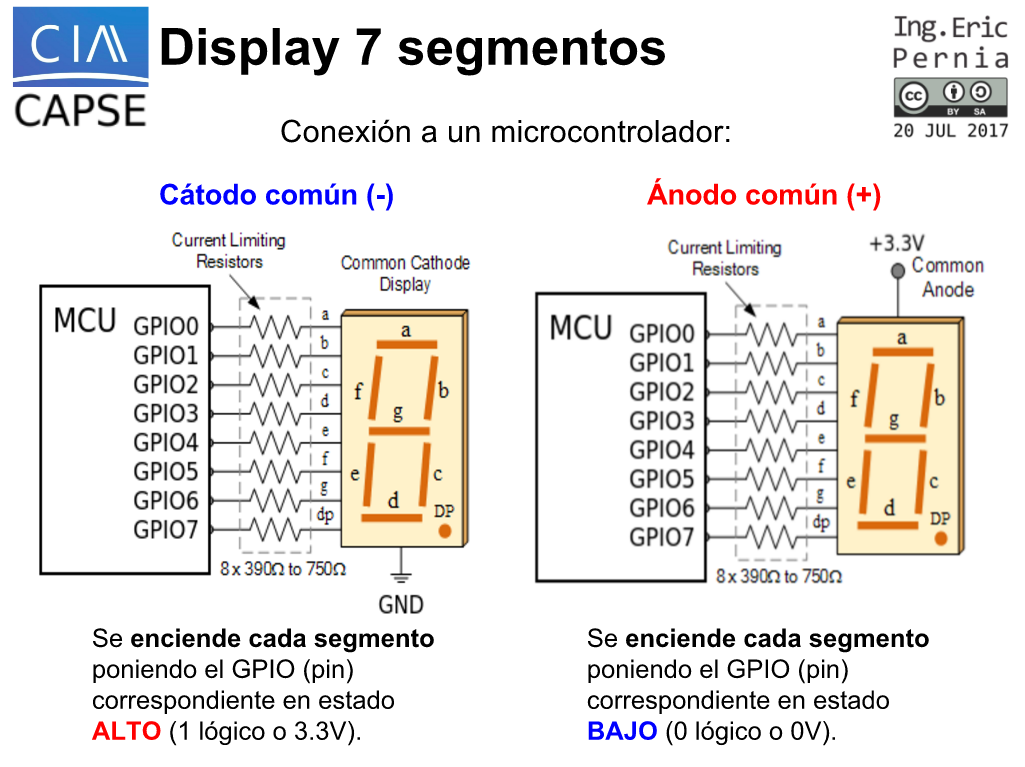
firmware_v3/examples/c/sapi/keypad_7segment/7 segment display - EDU-CIAA-NXP.png
