RamiroMadera/Proyecto_GENERATOR/firmware_v3/examples/c/sapi/lcd/lcd info/LCD HD44780 connection.png

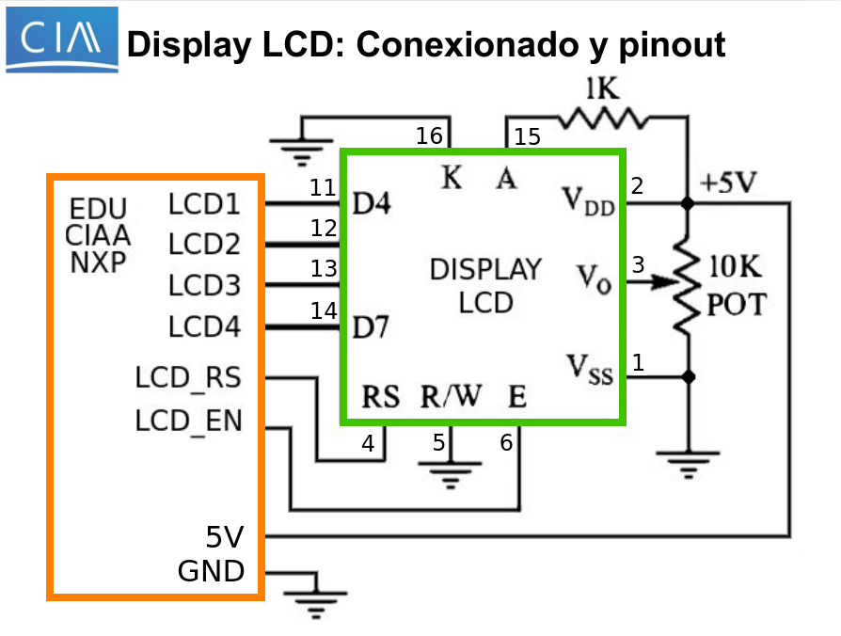
firmware_v3/examples/c/sapi/lcd/lcd info/LCD HD44780 connection.png
