RamiroMadera/Proyecto_GENERATOR/firmware_v3/examples/c/sapi/lcd/lcd_i2c/I2C expander PCF8574/Encapsulado en placa.png

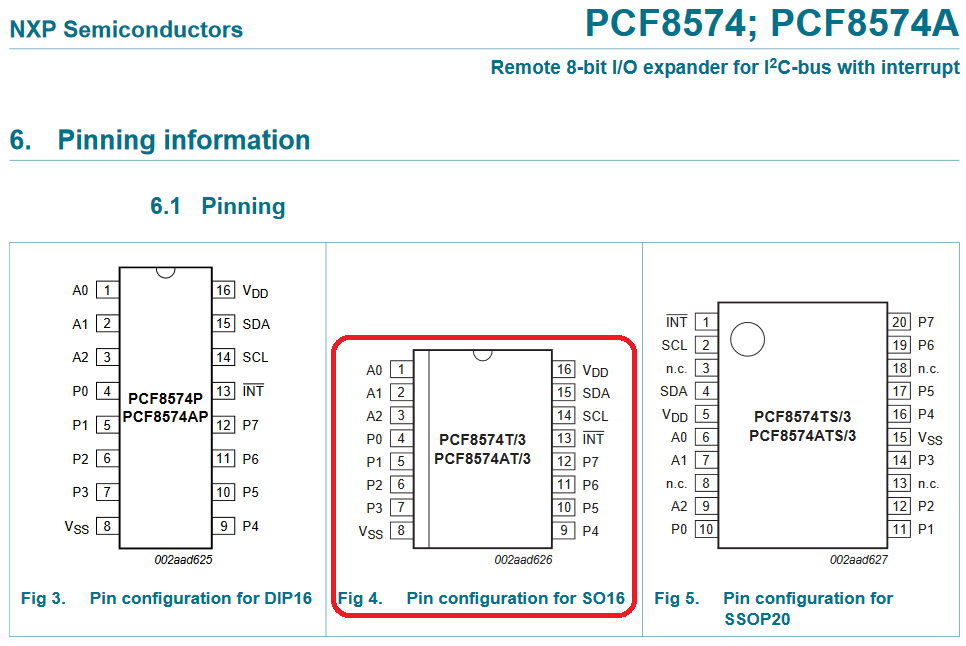
firmware_v3/examples/c/sapi/lcd/lcd_i2c/I2C expander PCF8574/Encapsulado en placa.png
