RamiroMadera/Proyecto_GENERATOR/firmware_v3/examples/c/sapi/servo/servo_pins.png

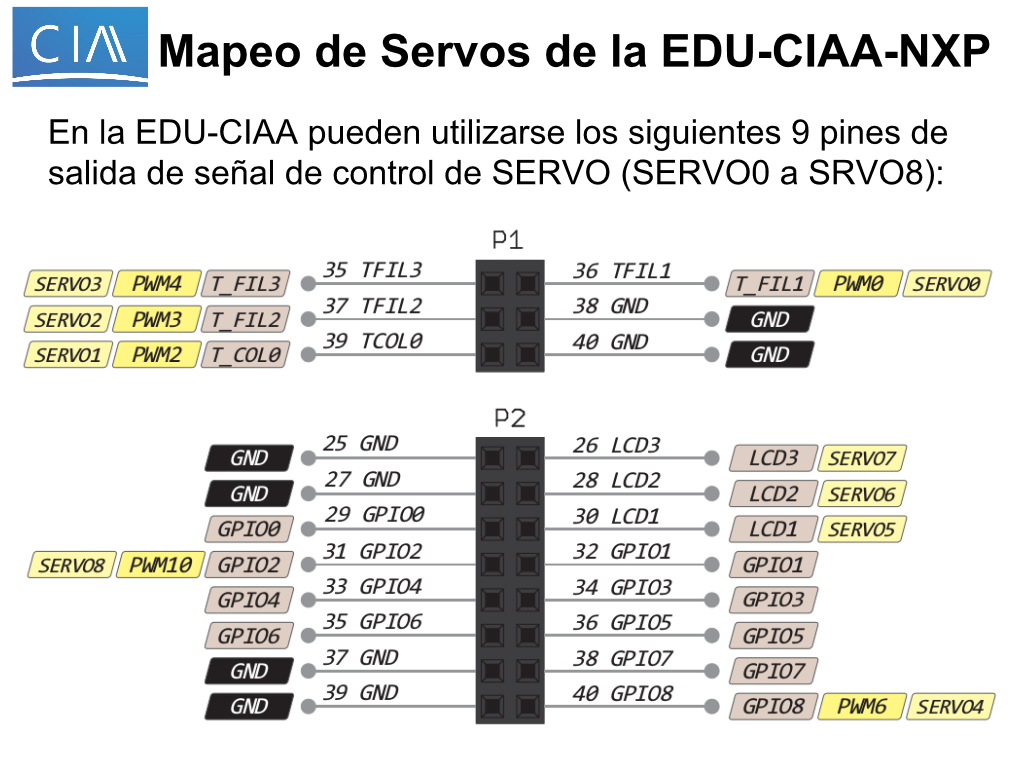
firmware_v3/examples/c/sapi/servo/servo_pins.png
