RamiroMadera/Proyecto_GENERATOR/firmware_v3/examples/c/sapi/wifi/esp8266/Conexion ESP8266 y EDU-CIAA.png

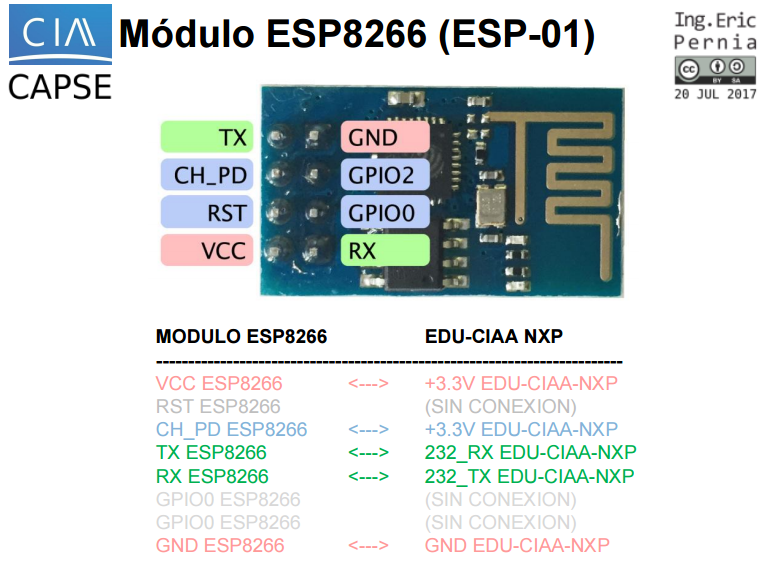
firmware_v3/examples/c/sapi/wifi/esp8266/Conexion ESP8266 y EDU-CIAA.png
