RamiroMadera/Proyecto_GENERATOR/firmware_v3/examples/c/sapi/wifi/esp8266/iot_thingspeak/Datos en Thingspeak.png

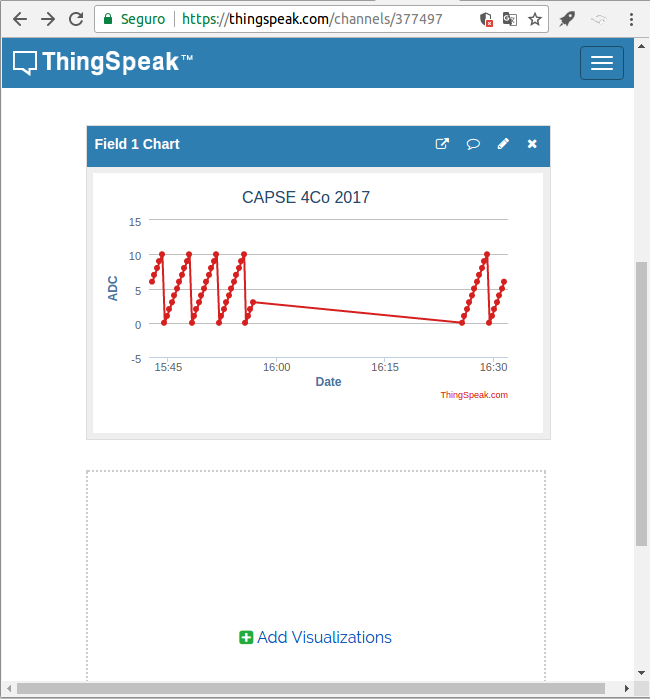
firmware_v3/examples/c/sapi/wifi/esp8266/iot_thingspeak/Datos en Thingspeak.png
