RamiroMadera/Proyecto_GENERATOR/firmware_v3/documentation/firmware/usage/program_strcuture.png

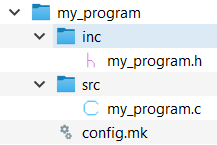
firmware_v3/documentation/firmware/usage/program_strcuture.png
