RamiroMadera/Proyecto_GENERATOR/firmware_v3/documentation/firmware/usage/user_preferences.png

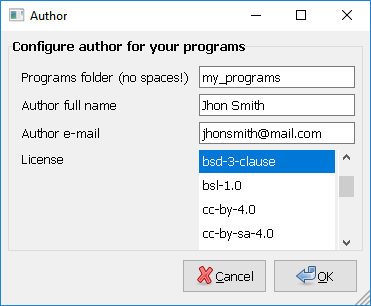
firmware_v3/documentation/firmware/usage/user_preferences.png
