RamiroMadera/Proyecto_GENERATOR/firmware_v3/documentation/CIAA_Boards/NXP_LPC4337/EDU-CIAA-NXP/EDU-CIAA-NXP v1.1 Board - 2019-01-03 v5r0.pdf

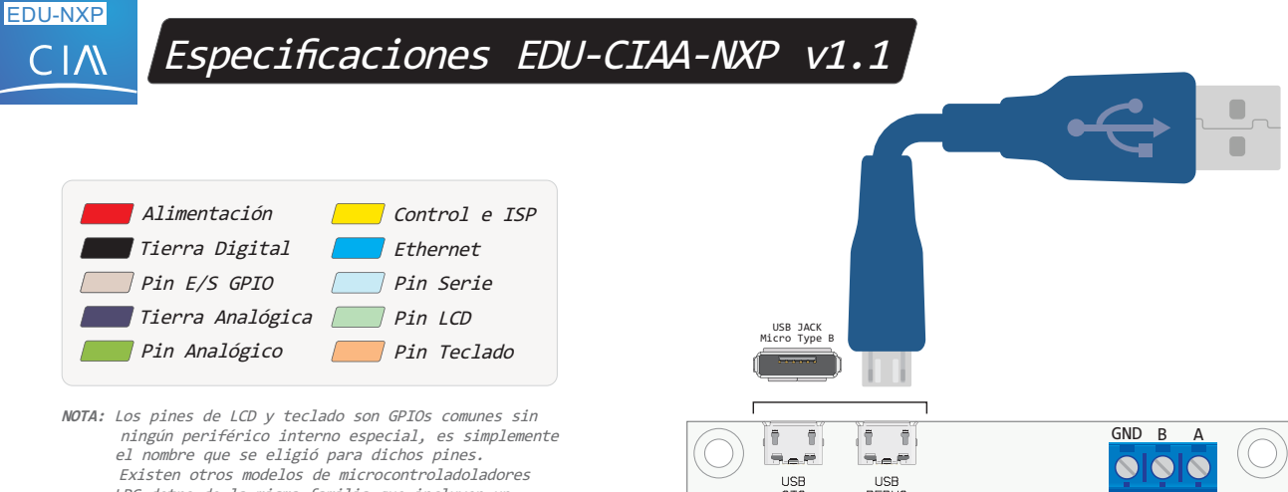
[picture p150: figure]
GND B; Alimentación; Tierra Digital; Pin Analógico; Tierra Analógica; Pin E/S GPIO; Pin Serie; Control e ISP; Pin LCD; Pin Teclado; Ethernet; Especificaciones EDU-CIAA-NXP v1.1; Existen otros modelos de microcontroladoladores; EDU-NXP; USB JACK Micro Type B

03 ENE 2019
ver 5 rev 0

# Pernia

# Ing.Eric

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
### Tira de 40 pines hembra de 0.1"(2,54 mm) de espaciado

## GND

## GND GND GND GND GND

## GNDA GNDA GNDA GNDA GNDA GNDA

## WAKEUP

5V

## TCOL2 TFIL1

## GND

## GND

## GND

## GND

## TCOL1 TFIL0 TFIL3 TFIL2 TCOL0

## GNDA

## ISP

## RESET

CH3
CH2
CH1

## DAC VDDA

3V3

I2C_SDA

I2C_SCL

RS232_RX

RS232_TX

CAN_RD

CAN_TD

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
### Tira de 40 pines hembra de 0.1"(2,54 mm) de espaciado

## GPIO2 GPIO4 GPIO6 GND

## GND

## GND

## GND

## GND

## GND

## GND

## GND

## GND

## GND

## GND

## GPIO0

## GPIO8

## GPIO7

## GPIO5

## GPIO3

## GPIO1

## LCD1

## LCD2

## LCD3

LCD_EN | LCD_RS LCD4

SPI_MISO

SPI_SCK

## TXD1

## TXD0

## MDIO

## CRS_DV

## MDC

## TX_EN

## RXD1

### REF_CLK

## RXD0

3V3 | 5V

SPI_MOSI

NOTA: Los pines de LCD y teclado son GPIOs comunes sin ningún periférico interno especial, es simplemente el nombre que se eligió para dichos pines.

LPC detro de la misma familia que incluyen un periférico para control de LCD gráfico (que el LPC 4337 no incluye) lo cual conlleva a confusiones.

Jumpers RS485
JP1 - Abierto permite recibir un eco local de lo transmitido.
Cortocircuitar para no recibir eco (default). JP2, JP3 y JP4 - Cortocircuitar en caso que
sea el último nodo de la red.

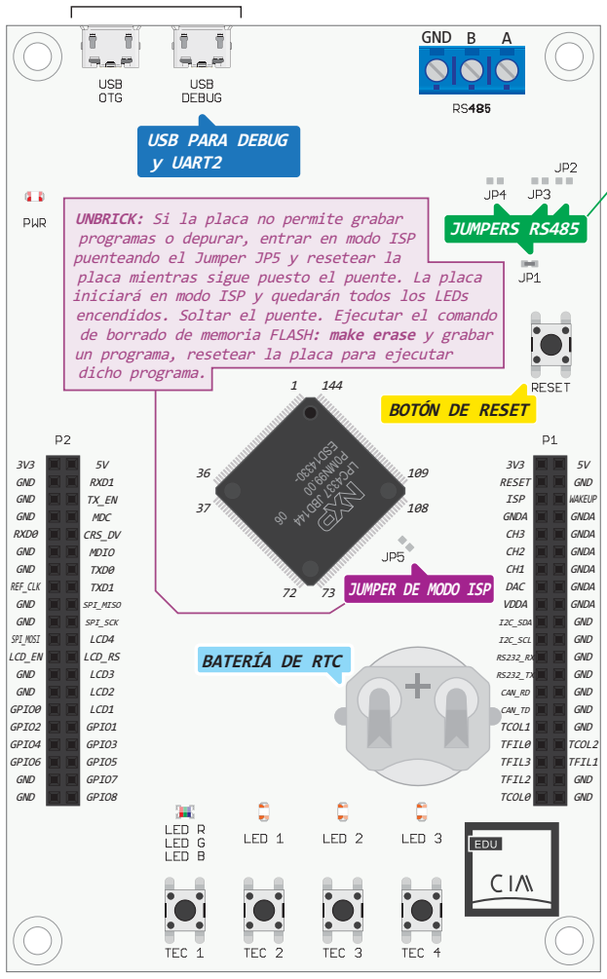
[picture p151: figure]
BOTÓN DE RESET; JUMPER DE MODO ISP; USB PARA DEBUG y UART2; JUMPERS RS485; LPC4337 JBD144; ESD14330-; BATERÍA DE RTC; GND; GND GND GND GND GND; GNDA GNDA GNDA GNDA GNDA GNDA; WAKEUP; TCOL2 TFIL1; GPIO8; GPIO7; GPIO5; GPIO3; GPIO1; LCD1; LCD2; LCD3; LCD_RS; LCD4; SPI_MISO; SPI_SCK; TXD1; TXD0; MDIO; CRS_DV; MDC; RXD1; GPIO2 GPIO4 GPIO6 GND; GPIO0; LCD_EN; REF_CLK; RXD0; SPI_MOSI; TCOL1 TFIL0 TFIL3 TFIL2 TCOL0; GNDA; ISP; RESET; CH3 CH2 CH1 DAC VDDA; I2C_SDA; I2C_SCL; CAN_RD; CAN_TD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

placa mientras sigue puesto el puente. La placa iniciará en modo ISP y quedarán todos los LEDs encendidos. Soltar el puente. Ejecutar el comando de borrado de memoria FLASH: make erase y grabar un programa, resetear la placa para ejecutar

# EDU-CIAA-NXP v1.1 Pines utilizados del NXP LPC4337 JBD144 (1 a 72)

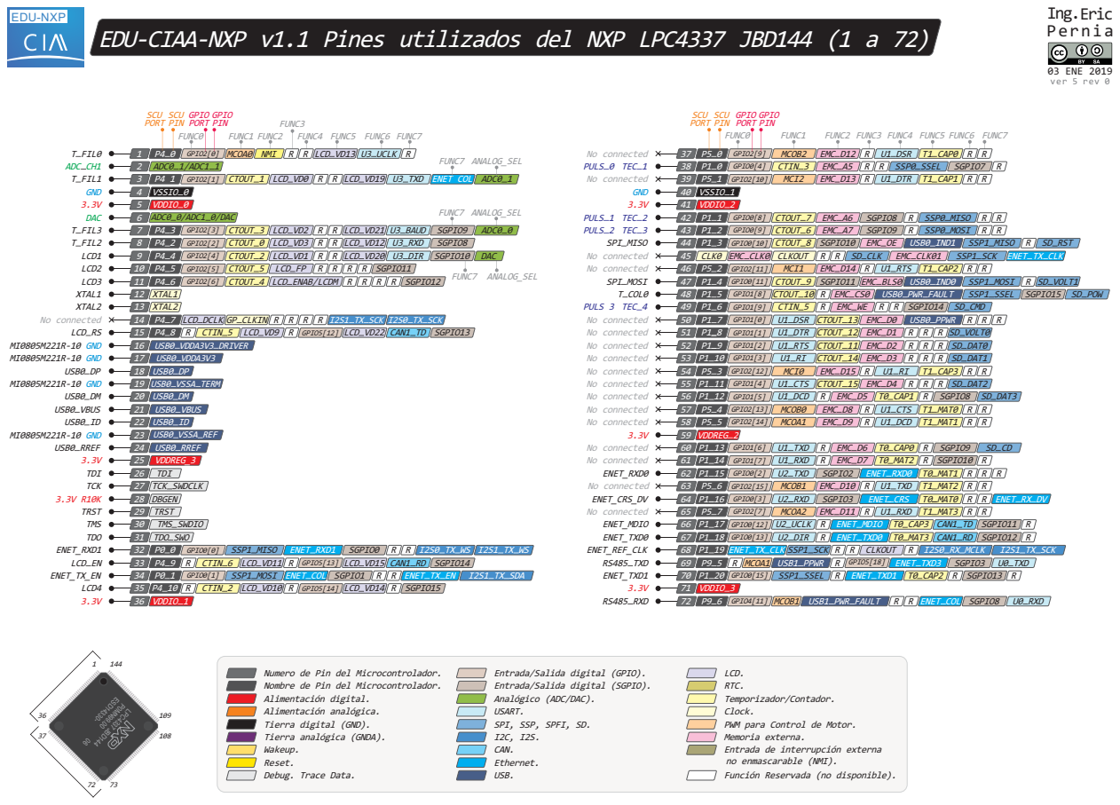
[picture p152: page 2]

LCD DCLK GP CLKIN R R R R

I2S1 TX SCK I2S0 TX SCK

Numero de Pin del Microcontrolador.
Nombre de Pin del Microcontrolador.
Alimentación digital.
Alimentación analógica.
Tierra digital (GND).
Tierra analógica (GNDA).
Wakeup.
Debug. Trace Data.

Entrada/Salida digital (GPIO).
Entrada/Salida digital (SGPIO).
USART.
SPI, SSP, SPFI, SD.
CAN.
Ethernet.
USB.

Clock.
PWM para Control de Motor.
Memoria externa.
Entrada de interrupción externa

Función Reservada (no disponible).

# EDU-CIAA-NXP v1.1 Pines utilizados del NXP LPC4337 JBD144 (73 a 144)

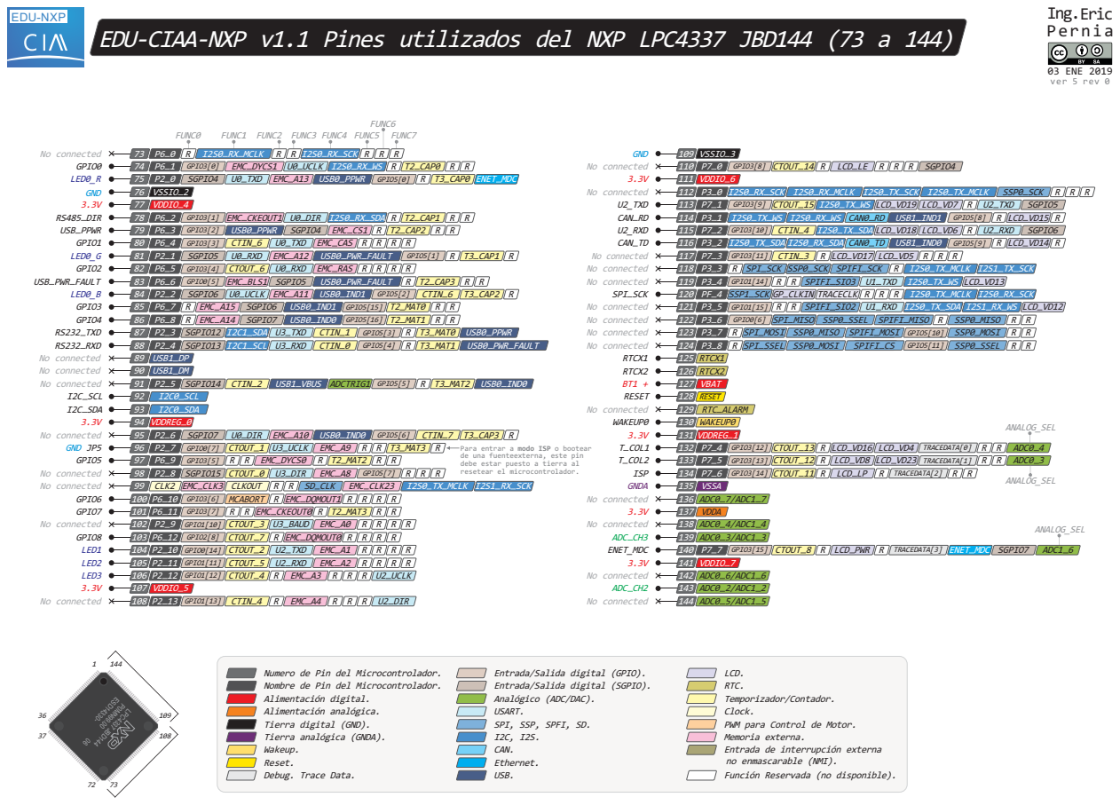
[picture p153: page 3]

de una fuenteexterna, este pin
debe estar puesto a tierra al
resetear el microcontrolador.

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

Entrada/Salida digital (GPIO).
Entrada/Salida digital (SGPIO).
USART.
SPI, SSP, SPFI, SD.
CAN.
Ethernet.
USB.

Clock.
PWM para Control de Motor.
Memoria externa.
Entrada de interrupción externa

Función Reservada (no disponible).
