RamiroMadera/Proyecto_GENERATOR/firmware_v3/documentation/CIAA_Boards/NXP_LPC54102/Pico-CIAA/picoCIAA v1.0 Board - 2019-01-08 v1r0.pdf

# Pernia

# Ing.Eric

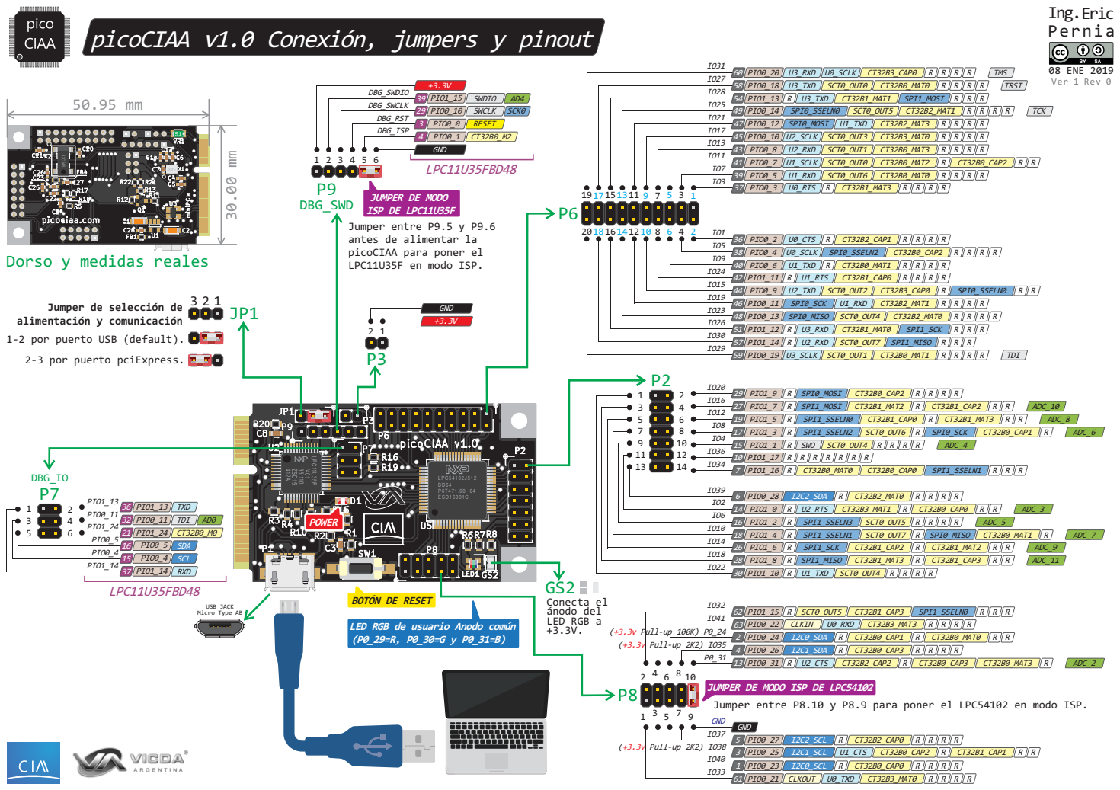
[picture p154: page 1]
08 ENE 2019 Ver 1 Rev 0; LPC5 4 1 0 2 J 5 1 2 BD6 4 P6T4 7 1 . 0 0 0 4 ESD1 6 0 9 1C; LPC11U35F; ZSD15; NXP; Conecta el ánodo del LED RGB a; POWER; 1 PIO0_23 I2C0_SCL R CT32B0_CAP0 R R R R; 5 PIO0_27 I2C2_SCL R CT32B2_CAP0 R R R R; 3 PIO0_25 I2C1_SCL; U1_CTS; CT32B0_CAP2 R CT32B1_CAP1 R R; (+3.3v Pull-up 2K2) IO38; GND; 61 PIO0_21 CLKOUT U0_TXD; CT32B3_MAT0 R R R R; 13 PIO0_31 R U2_CTS; CT32B2_CAP2 R CT32B0_CAP3; CT32B0_MAT3 R; ADC_2; 2 PIO0_24 I2C0_SDA R CT32B0_CAP1 R CT32B0_MAT0 R R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

picoCIAA v1.0 Conexión, jumpers y pinout

JUMPER DE MODO
ISP DE LPC11U35F
Jumper entre P9.5 y P9.6
antes de alimentar la
picoCIAA para poner el
LPC11U35F en modo ISP.

Dorso y medidas reales

Jumper de selección de
alimentación y comunicación
1-2 por puerto USB (default).
2-3 por puerto pciExpress.

BOTÓN DE RESET

USB JACK
Micro Type AB

+3.3V. LED RGB de usuario Anodo común

JUMPER DE MODO ISP DE LPC54102
Jumper entre P8.10 y P8.9 para poner el LPC54102 en modo ISP.
GND

# picoCIAA v1.0 Pines utilizados del NXP LPC54102J512 BD64

# Pernia

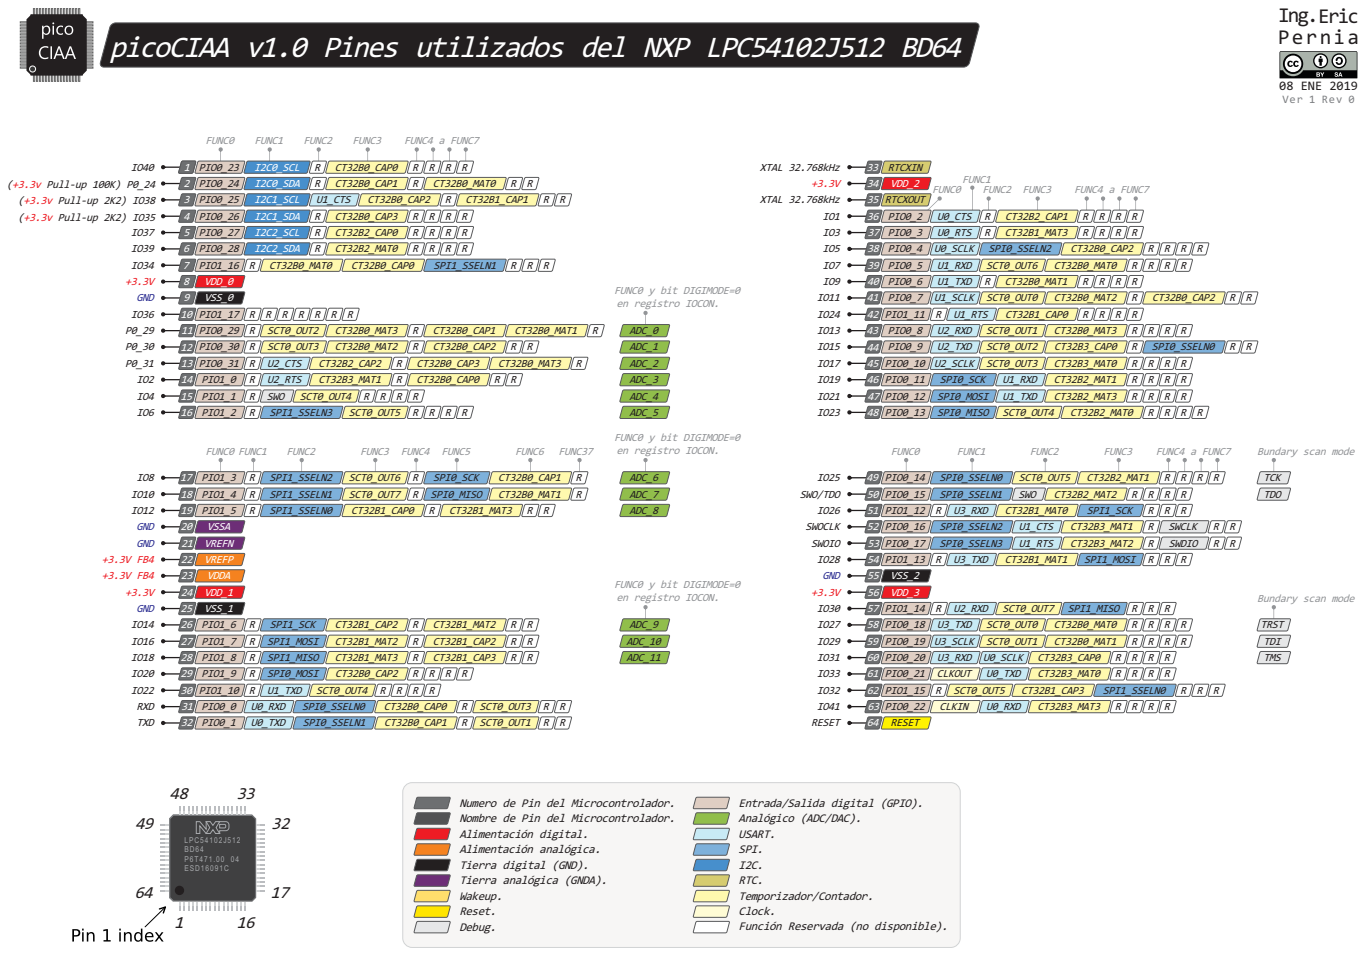
[picture p155: page 2]
LPC5 4 1 0 2 J 5 1 2 BD6 4 P6T4 7 1 . 0 0 0 4 ESD1 6 0 9 1C; 08 ENE 2019 Ver 1 Rev 0; Ing.Eric; FUNC0; FUNC1; FUNC2; FUNC3; FUNC4 a FUNC7; PIO0_23 I2C0_SCL; I2C1_SCL; I2C2_SCL; I2C0_SDA; I2C1_SDA; I2C2_SDA; U2_CTS; U1_CTS; U2_RTS; SPI1_SSELN3; SPI1_SSELN1; SCT0_OUT4 SCT0_OUT5; SCT0_OUT3; SCT0_OUT2; CT32B0_CAP0; CT32B0_MAT0; CT32B2_CAP0; CT32B0_CAP1 CT32B0_CAP2 CT32B0_CAP3; CT32B2_MAT0; ADC_0 ADC_1 ADC_2 ADC_3 ADC_4 ADC_5; CT32B1_CAP1; CT32B0_MAT3 CT32B0_MAT2; CT32B0_CAP1 CT32B0_CAP2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

FUNC0 y bit DIGIMODE=0
en registro IOCON.

Bundary scan mode

Numero de Pin del Microcontrolador.
Nombre de Pin del Microcontrolador.
Alimentación digital.
Alimentación analógica.
Tierra digital (GND).
Tierra analógica (GNDA).
Wakeup.
Reset.
Debug.

Entrada/Salida digital (GPIO).
Analógico (ADC/DAC).
USART.
SPI.
RTC.
Temporizador/Contador.
Clock.
Función Reservada (no disponible).
