RamiroMadera/Proyecto_GENERATOR/firmware_v3/documentation/CIAA_Boards/Silabs_EFM32HG322_F64/CIAA-Z3R0/CIAA-Z3R0 v0.1 Board - 2018-12-24 v2r0.pdf

## Pernia

## Ing.Eric

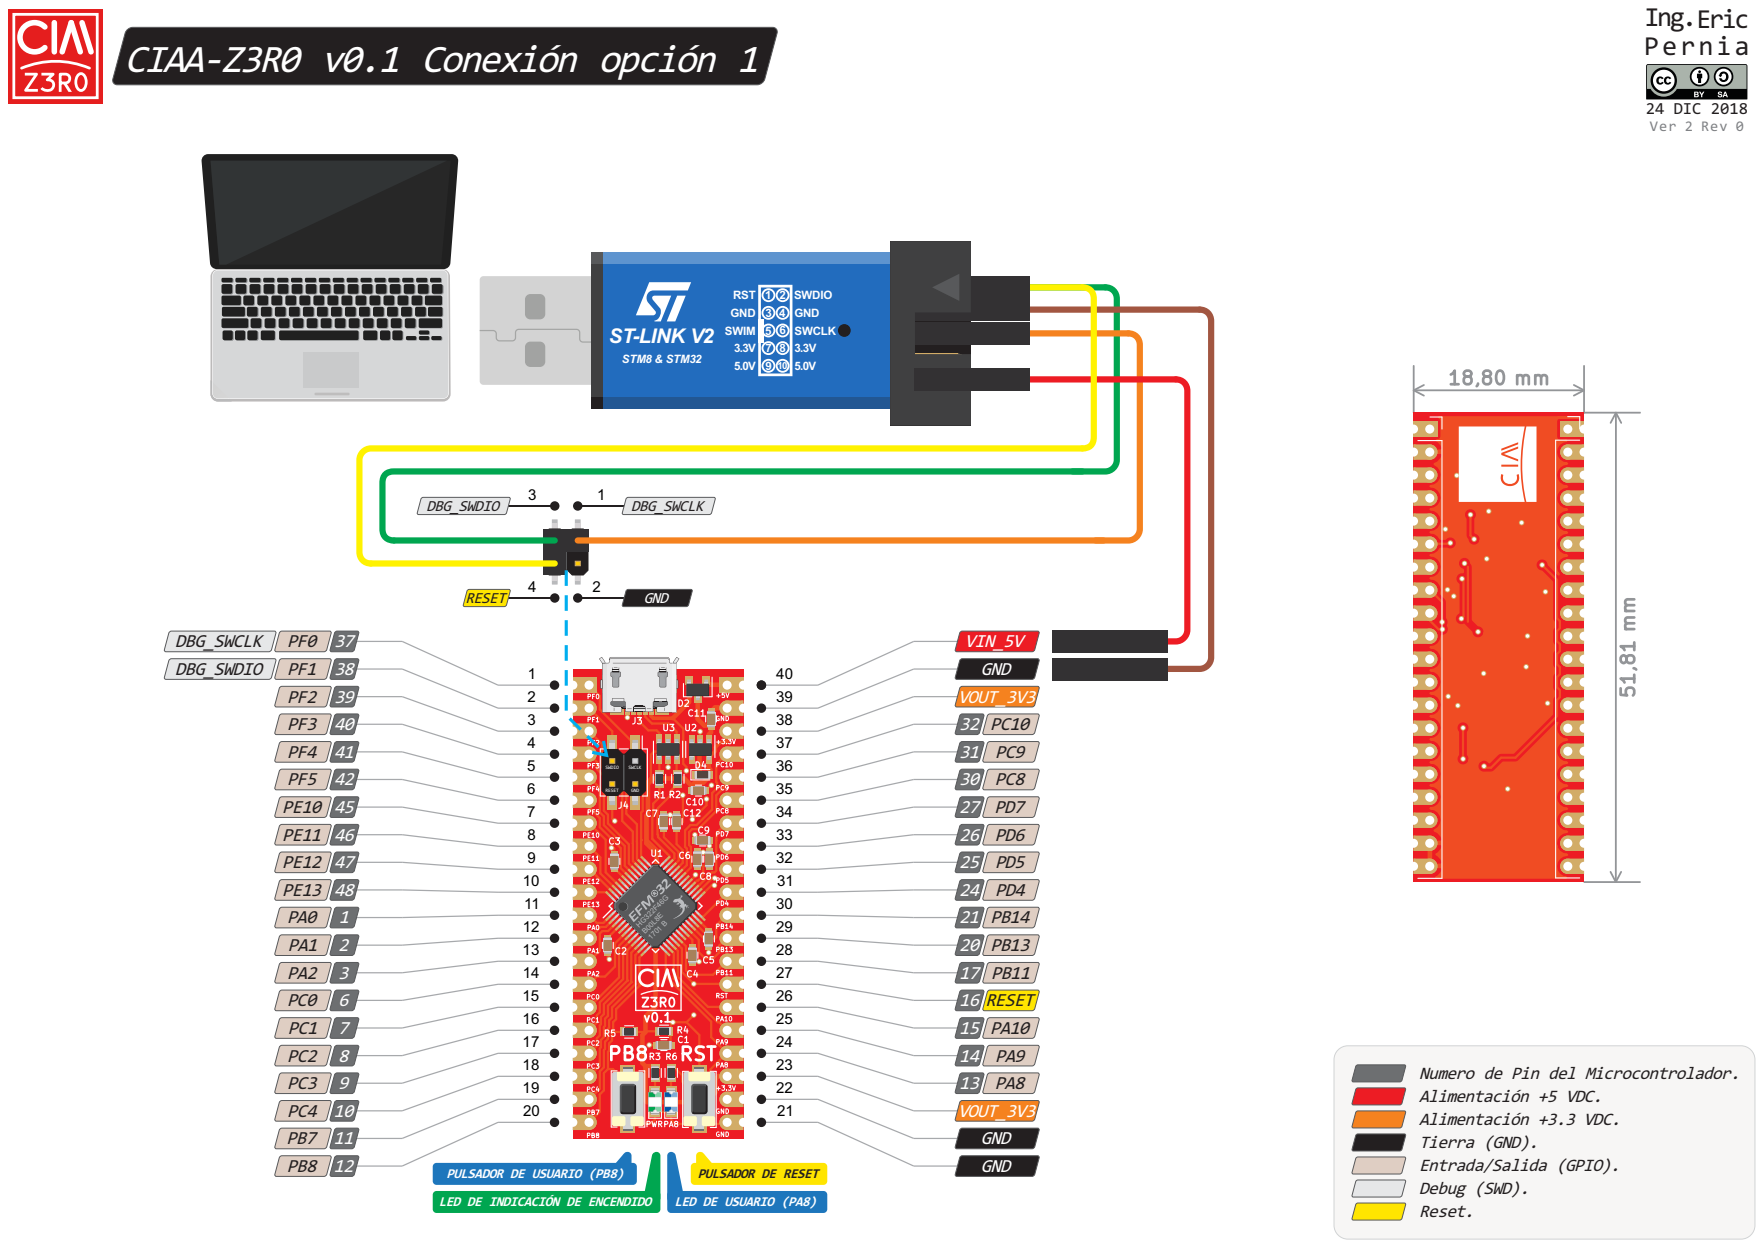
[picture p156: page 1]
24 DIC 2017; Ver; Rev 1; Pernia; Ing.Eric; GND; SWCLK; RESET; SWDIO; ST-LINK V2; STM8 & STM32; RST; SWIM; DBG_SWCLK DBG_SWDIO; DBG_SWDIO; DBG_SWCLK; PULSADOR DE USUARIO (PB8); PULSADOR DE RESET; LED DE INDICACIÓN DE ENCENDIDO; LED DE USUARIO (PA8); PC10 PC9 PC8 PD7 PD6 PD5 PD4 PB14 PB13 PB11 RESET PA10 PA9 PA8; VIN_5V; VOUT_3V3; VOUT_3V3 GND; 24 DIC 2018 Ver 2 Rev 0

CIAA-Z3R0 v0.1 Conexión opción 1

Pernia Ing.Eric

24 DIC 2017 Ver 1 Rev 0

Numero de Pin del Microcontrolador.
Alimentación +5 VDC.
Alimentación +3.3 VDC.
Tierra (GND).
Entrada/Salida (GPIO).
Debug (SWD).
Reset.

# CIAA-Z3R0 v0.1 Conexión opción 2

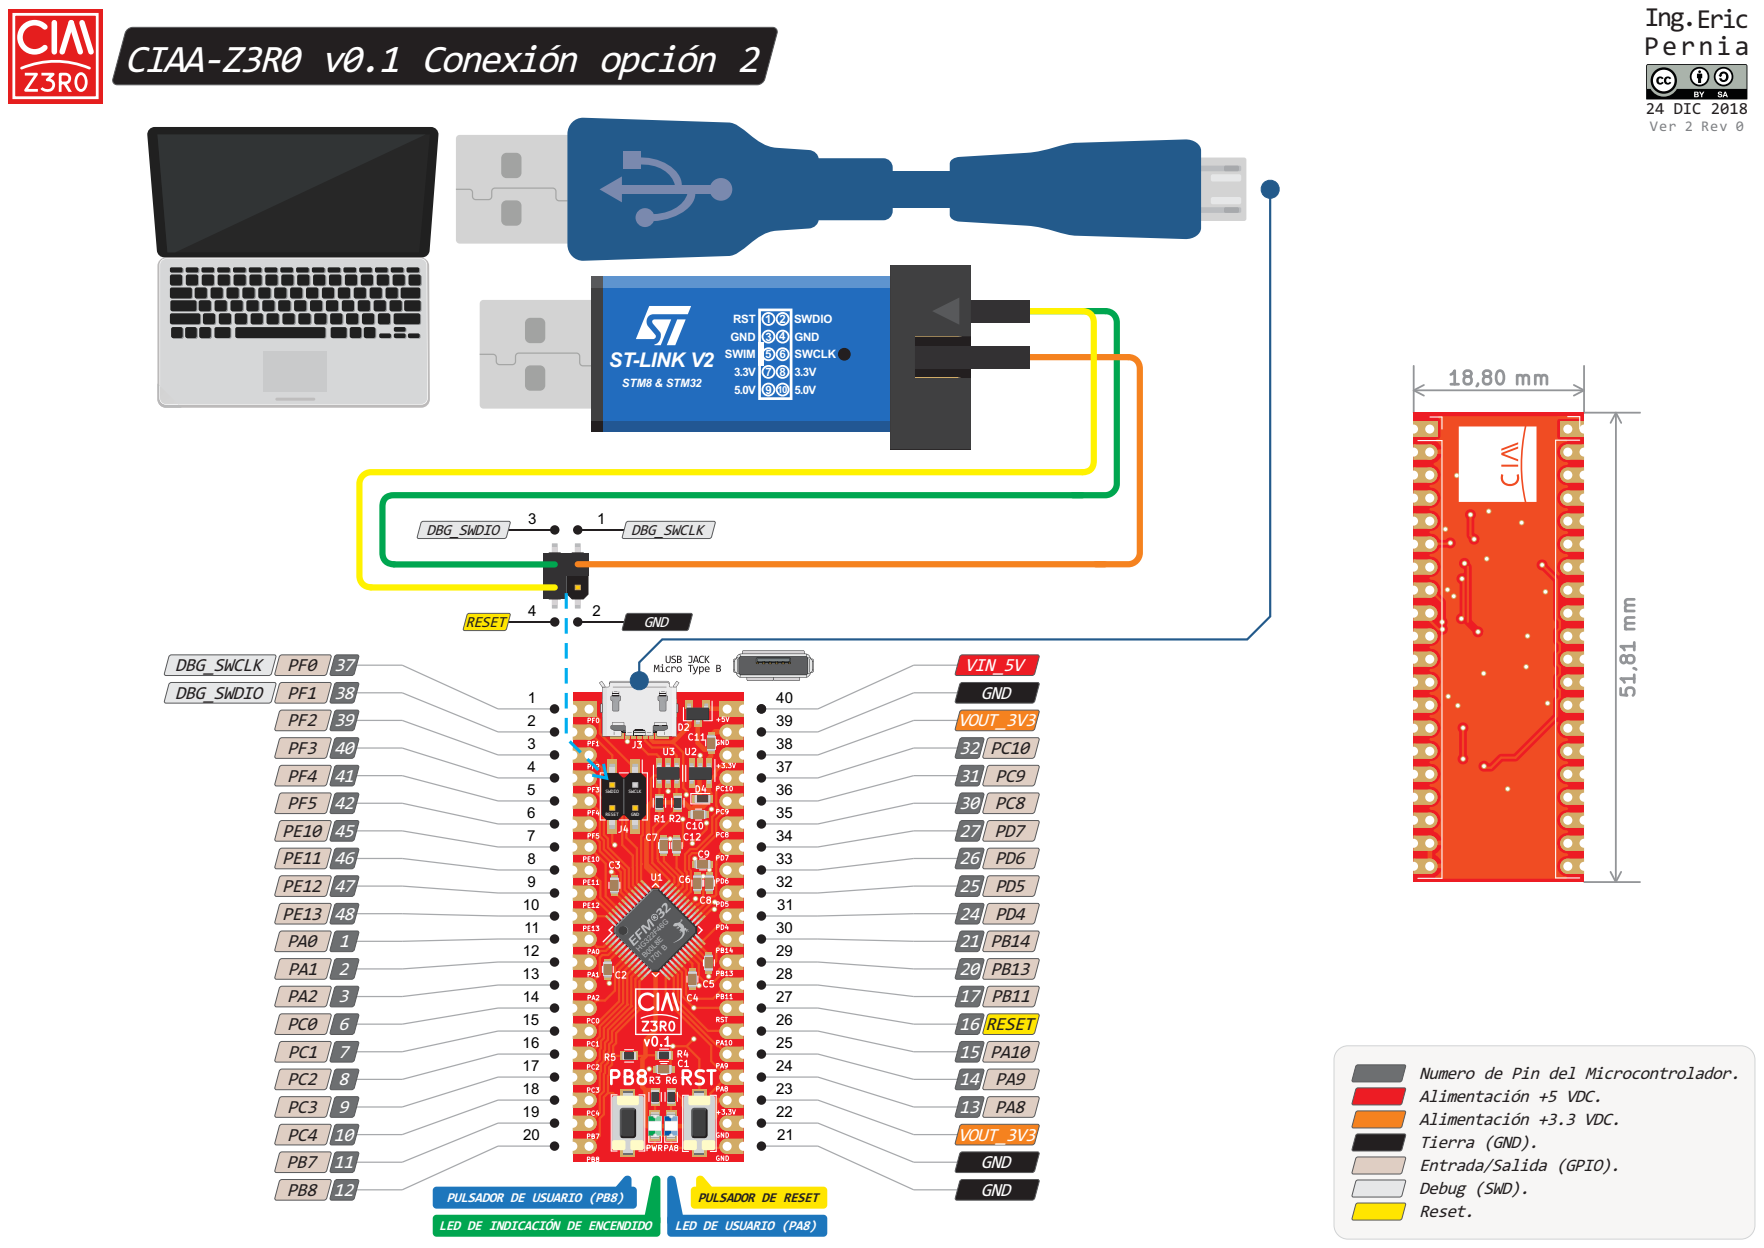
[picture p157: page 2]
24 DIC 2017; Ver; Rev 1; Pernia; Ing.Eric; GND; SWCLK; RESET; SWDIO; ST-LINK V2; STM8 & STM32; RST; SWIM; DBG_SWCLK DBG_SWDIO; PC10 PC9 PC8 PD7 PD6 PD5 PD4 PB14 PB13 PB11 RESET PA10 PA9 PA8; VIN_5V; VOUT_3V3; VOUT_3V3 GND; DBG_SWDIO; DBG_SWCLK; 24 DIC 2018 Ver 2 Rev 0; PULSADOR DE USUARIO (PB8); PULSADOR DE RESET; LED DE INDICACIÓN DE ENCENDIDO; LED DE USUARIO (PA8)

Pernia Ing.Eric

24 DIC 2017 Ver 1 Rev 0

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

# Microcontrolador Silicon Labs EFM322 HG322F64G-B-QFP48

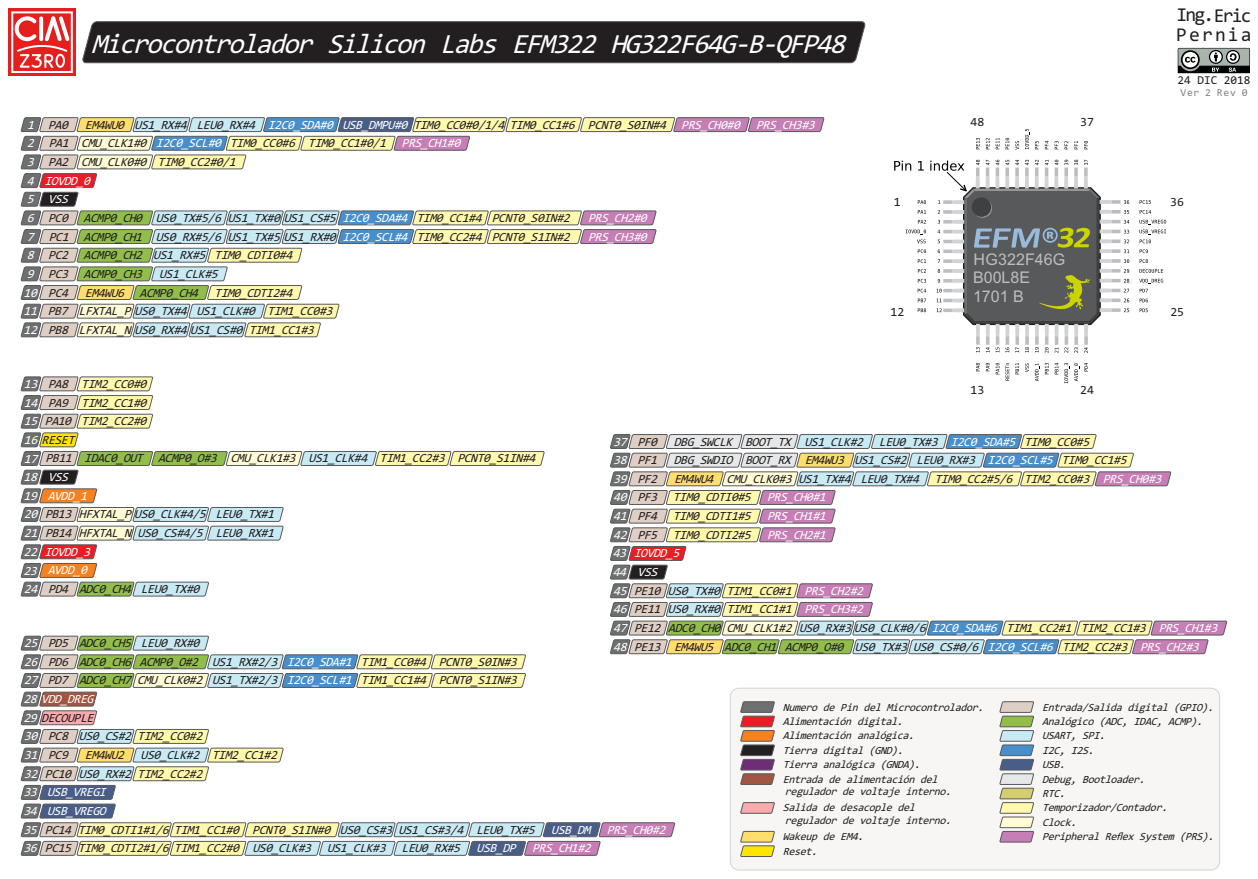
[picture p158: page 3]
Numero de Pin del Microcontrolador.; Entrada/Salida digital (GPIO).; 10 PC4 EM4WU6 ACMP0_CH4 TIM0_CDTI2#4 11 PB7 LFXTAL_P US0_TX#4 US1_CLK#0 TIM1_CC0#3 12 PB8 LFXTAL_N US0_RX#4 US1_CS#0 TIM1_CC1#3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

Alimentación digital.
Alimentación analógica.
Tierra digital (GND).
Tierra analógica (GNDA).
Entrada de alimentación del
regulador de voltaje interno.
Salida de desacople del
Wakeup de EM4.

Analógico (ADC, IDAC, ACMP).
USART, SPI.
USB.
Debug, Bootloader.
RTC.
Temporizador/Contador.
Clock.
Peripheral Reflex System (PRS).

# CIAA-Z3R0 v0.1 Pines utilizados del Silicon Labs EFM32 HG322F64G-B-QFP48

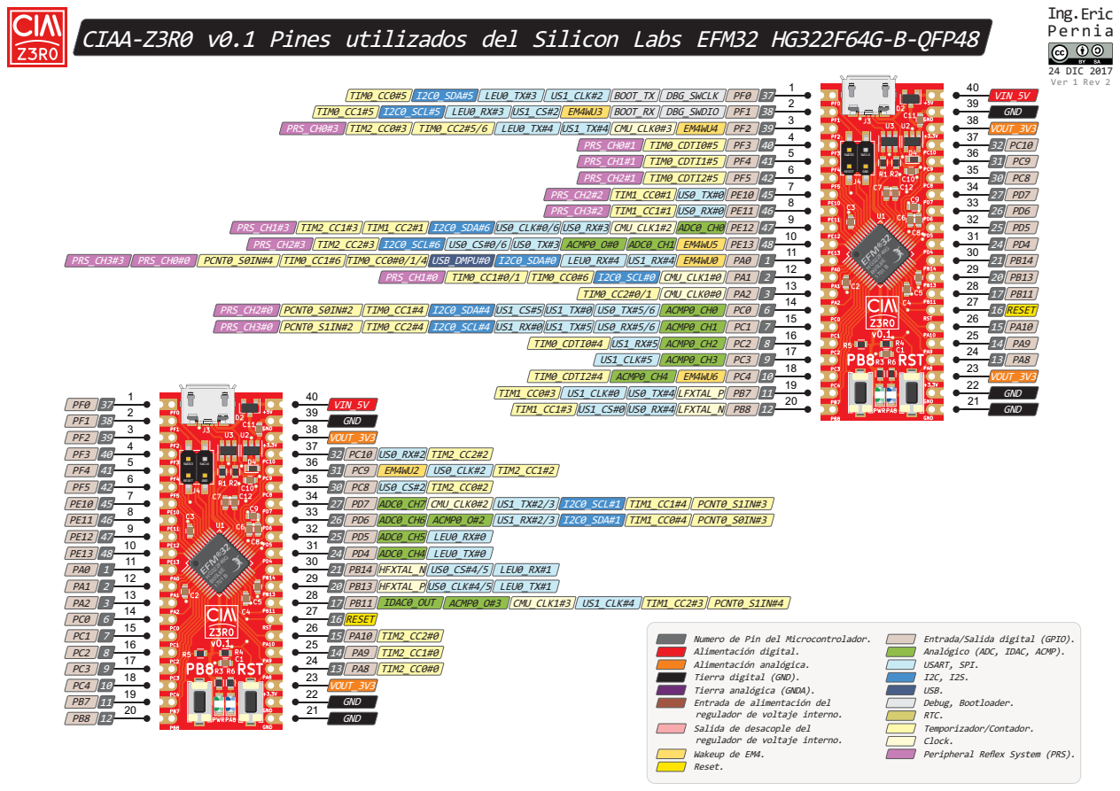
[picture p159: page 4]
24 DIC 2017; Ver; Rev 1; Pernia; Ing.Eric; GND; SWCLK; RESET; SWDIO; PC10 PC9 PC8 PD7 PD6 PD5 PD4 PB14 PB13 PB11 RESET PA10 PA9 PA8; VIN_5V; VOUT_3V3; VOUT_3V3 GND; 24 DIC 2017 Ver 1 Rev 2; Numero de Pin del Microcontrolador.; Entrada/Salida digital (GPIO).; PRS_CH2#3 TIM2_CC2#3 I2C0_SCL#6 US0_CS#0/6 US0_TX#3 ACMP0_O#0 ADC0_CH1 EM4WU5; PRS_CH1#3 TIM2_CC1#3 TIM1_CC2#1 I2C0_SDA#6 US0_CLK#0/6 US0_RX#3 CMU_CLK1#2 ADC0_CH0; PRS_CH3#2 TIM1_CC1#1 US0_RX#0; PRS_CH2#2 TIM1_CC0#1 US0_TX#0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
