RamiroMadera/Proyecto_GENERATOR/kicad/GENERATOR_PCB_LISTO.pdf

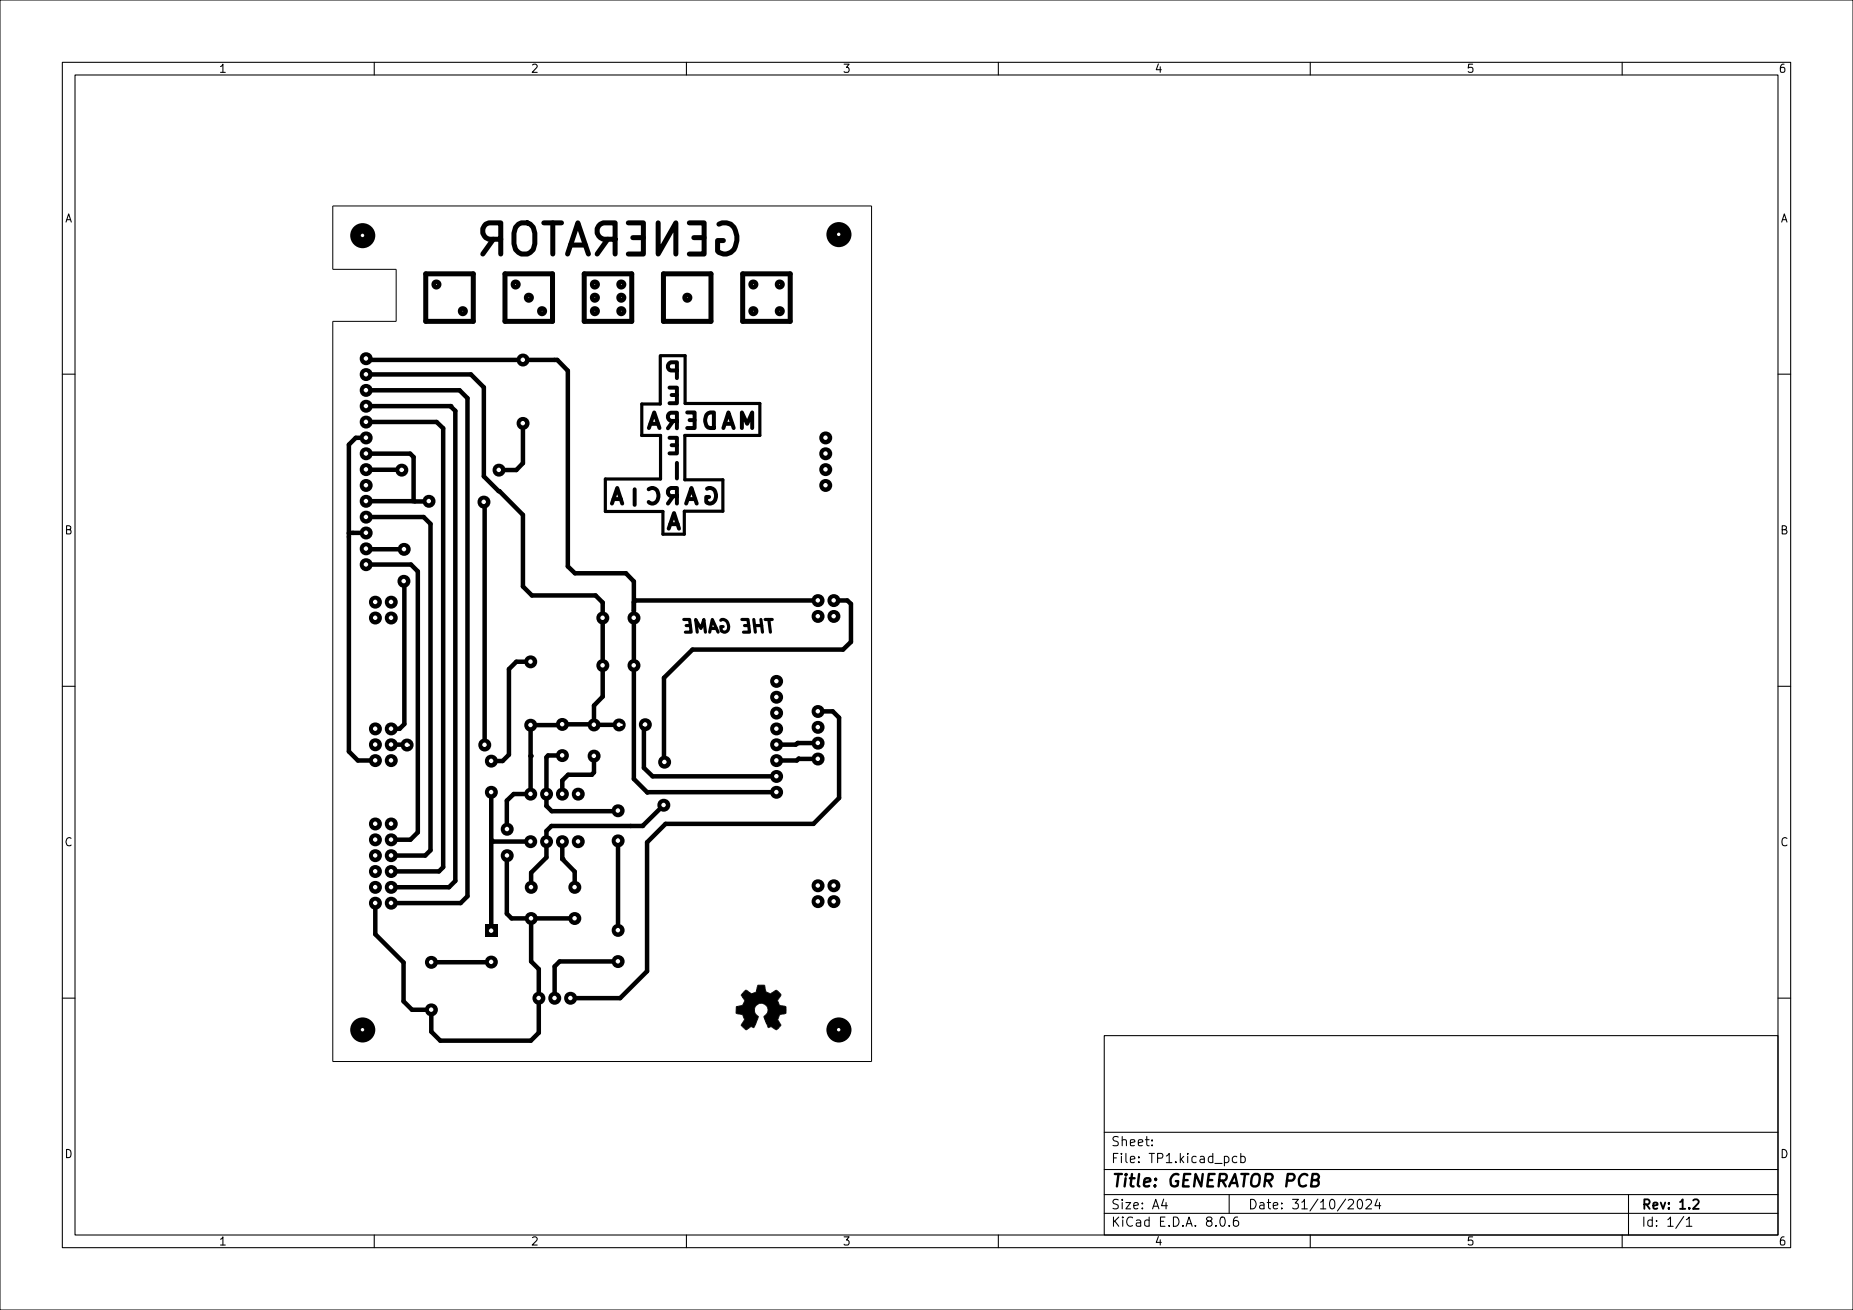
[picture p164: page 1]
