RamiroMadera/Proyecto_GENERATOR/firmware_v3/examples/c/app/GFX_Adafruit/ILI9341_ADA.c

///////////////////////////////////////////////////////////////////////////
////                                                                   ////
////                              ILI9341.c                            ////
////                                                                   ////
////               ILI9341 display driver for CCS C compiler           ////
////                                                                   ////
///////////////////////////////////////////////////////////////////////////
////                                                                   ////
////               This is a free software with NO WARRANTY.           ////
////                     https://simple-circuit.com/                   ////
////                                                                   ////
///////////////////////////////////////////////////////////////////////////
/*
 * This library works with the Adafruit 2.8" Touch Shield V2 (SPI)
 *    http://www.adafruit.com/products/1651
 * Adafruit 2.4" TFT LCD with Touchscreen Breakout w/MicroSD Socket - ILI9341
 *    https://www.adafruit.com/product/2478
 * 2.8" TFT LCD with Touchscreen Breakout Board w/MicroSD Socket - ILI9341
 *    https://www.adafruit.com/product/1770
 * 2.2" 18-bit color TFT LCD display with microSD card breakout - ILI9340
 *    https://www.adafruit.com/product/1770
 * TFT FeatherWing - 2.4" 320x240 Touchscreen For All Feathers
 *    https://www.adafruit.com/product/3315
 *
 * These displays use SPI to communicate, 4 or 5 pins are required
 * to interface (RST is optional).
 *
 * Adafruit invests time and resources providing this open source code,
 * please support Adafruit and open-source hardware by purchasing
 * products from Adafruit!
 *
 *
 * This library depends on <a href="https://github.com/adafruit/Adafruit_GFX">
 * Adafruit_GFX</a> being present on your system. Please make sure you have
 * installed the latest version before using this library.
 *
 * Written by Limor "ladyada" Fried for Adafruit Industries.
 *
 * BSD license, all text here must be included in any redistribution.
 *
 */

#include <stdint.h>
#ifndef bool
#define bool int1
#endif

#define ILI9341_TFTWIDTH 240  ///< ILI9341 max TFT width
#define ILI9341_TFTHEIGHT 320 ///< ILI9341 max TFT height

#define ILI9341_NOP 0x00     ///< No-op register
#define ILI9341_SWRESET 0x01 ///< Software reset register
#define ILI9341_RDDID 0x04   ///< Read display identification information
#define ILI9341_RDDST 0x09   ///< Read Display Status

#define ILI9341_SLPIN 0x10  ///< Enter Sleep Mode
#define ILI9341_SLPOUT 0x11 ///< Sleep Out
#define ILI9341_PTLON 0x12  ///< Partial Mode ON
#define ILI9341_NORON 0x13  ///< Normal Display Mode ON

#define ILI9341_RDMODE 0x0A     ///< Read Display Power Mode
#define ILI9341_RDMADCTL 0x0B   ///< Read Display MADCTL
#define ILI9341_RDPIXFMT 0x0C   ///< Read Display Pixel Format
#define ILI9341_RDIMGFMT 0x0D   ///< Read Display Image Format
#define ILI9341_RDSELFDIAG 0x0F ///< Read Display Self-Diagnostic Result

#define ILI9341_INVOFF 0x20   ///< Display Inversion OFF
#define ILI9341_INVON 0x21    ///< Display Inversion ON
#define ILI9341_GAMMASET 0x26 ///< Gamma Set
#define ILI9341_DISPOFF 0x28  ///< Display OFF
#define ILI9341_DISPON 0x29   ///< Display ON

#define ILI9341_CASET 0x2A ///< Column Address Set
#define ILI9341_PASET 0x2B ///< Page Address Set
#define ILI9341_RAMWR 0x2C ///< Memory Write
#define ILI9341_RAMRD 0x2E ///< Memory Read

#define ILI9341_PTLAR 0x30    ///< Partial Area
#define ILI9341_MADCTL 0x36   ///< Memory Access Control
#define ILI9341_VSCRSADD 0x37 ///< Vertical Scrolling Start Address
#define ILI9341_PIXFMT 0x3A   ///< COLMOD: Pixel Format Set

#define ILI9341_FRMCTR1 0xB1 ///< Frame Rate Control (In Normal Mode/Full Colors)
#define ILI9341_FRMCTR2 0xB2 ///< Frame Rate Control (In Idle Mode/8 colors)
#define ILI9341_FRMCTR3 0xB3 ///< Frame Rate control (In Partial Mode/Full Colors)
#define ILI9341_INVCTR 0xB4  ///< Display Inversion Control
#define ILI9341_DFUNCTR 0xB6 ///< Display Function Control

#define ILI9341_PWCTR1 0xC0 ///< Power Control 1
#define ILI9341_PWCTR2 0xC1 ///< Power Control 2
#define ILI9341_PWCTR3 0xC2 ///< Power Control 3
#define ILI9341_PWCTR4 0xC3 ///< Power Control 4
#define ILI9341_PWCTR5 0xC4 ///< Power Control 5
#define ILI9341_VMCTR1 0xC5 ///< VCOM Control 1
#define ILI9341_VMCTR2 0xC7 ///< VCOM Control 2

#define ILI9341_RDID1 0xDA ///< Read ID 1
#define ILI9341_RDID2 0xDB ///< Read ID 2
#define ILI9341_RDID3 0xDC ///< Read ID 3
#define ILI9341_RDID4 0xDD ///< Read ID 4

#define ILI9341_GMCTRP1 0xE0 ///< Positive Gamma Correction
#define ILI9341_GMCTRN1 0xE1 ///< Negative Gamma Correction
// #define ILI9341_PWCTR6     0xFC

// Color definitions
#define ILI9341_BLACK 0x0000       ///<   0,   0,   0
#define ILI9341_NAVY 0x000F        ///<   0,   0, 123
#define ILI9341_DARKGREEN 0x03E0   ///<   0, 125,   0
#define ILI9341_DARKCYAN 0x03EF    ///<   0, 125, 123
#define ILI9341_MAROON 0x7800      ///< 123,   0,   0
#define ILI9341_PURPLE 0x780F      ///< 123,   0, 123
#define ILI9341_OLIVE 0x7BE0       ///< 123, 125,   0
#define ILI9341_LIGHTGREY 0xC618   ///< 198, 195, 198
#define ILI9341_DARKGREY 0x7BEF    ///< 123, 125, 123
#define ILI9341_BLUE 0x001F        ///<   0,   0, 255
#define ILI9341_GREEN 0x07E0       ///<   0, 255,   0
#define ILI9341_CYAN 0x07FF        ///<   0, 255, 255
#define ILI9341_RED 0xF800         ///< 255,   0,   0
#define ILI9341_MAGENTA 0xF81F     ///< 255,   0, 255
#define ILI9341_YELLOW 0xFFE0      ///< 255, 255,   0
#define ILI9341_WHITE 0xFFFF       ///< 255, 255, 255
#define ILI9341_ORANGE 0xFD20      ///< 255, 165,   0
#define ILI9341_GREENYELLOW 0xAFE5 ///< 173, 255,  41
#define ILI9341_PINK 0xFC18        ///< 255, 130, 198

#define MADCTL_MY 0x80  ///< Bottom to top
#define MADCTL_MX 0x40  ///< Right to left
#define MADCTL_MV 0x20  ///< Reverse Mode
#define MADCTL_ML 0x10  ///< LCD refresh Bottom to top
#define MADCTL_RGB 0x00 ///< Red-Green-Blue pixel order
#define MADCTL_BGR 0x08 ///< Blue-Green-Red pixel order
#define MADCTL_MH 0x04  ///< LCD refresh right to left

#ifndef ILI9341_SPI_XFER
#define ILI9341_SPI_XFER(x) SPI_XFER(ILI9341, x)
#endif

uint16_t
    _width,  ///< Display width as modified by current rotation
    _height; ///< Display height as modified by current rotation
uint8_t
    rotation; ///< Display rotation (0 thru 3)

rom uint8_t initcmd[] = {
    0xEF, 3, 0x03, 0x80, 0x02,
    0xCF, 3, 0x00, 0xC1, 0x30,
    0xED, 4, 0x64, 0x03, 0x12, 0x81,
    0xE8, 3, 0x85, 0x00, 0x78,
    0xCB, 5, 0x39, 0x2C, 0x00, 0x34, 0x02,
    0xF7, 1, 0x20,
    0xEA, 2, 0x00, 0x00,
    ILI9341_PWCTR1, 1, 0x23,       // Power control VRH[5:0]
    ILI9341_PWCTR2, 1, 0x10,       // Power control SAP[2:0];BT[3:0]
    ILI9341_VMCTR1, 2, 0x3e, 0x28, // VCM control
    ILI9341_VMCTR2, 1, 0x86,       // VCM control2
    ILI9341_MADCTL, 1, 0x48,       // Memory Access Control
    ILI9341_VSCRSADD, 1, 0x00,     // Vertical scroll zero
    ILI9341_PIXFMT, 1, 0x55,
    ILI9341_FRMCTR1, 2, 0x00, 0x18,
    ILI9341_DFUNCTR, 3, 0x08, 0x82, 0x27,                    // Display Function Control
    0xF2, 1, 0x00,                                           // 3Gamma Function Disable
    ILI9341_GAMMASET, 1, 0x01,                               // Gamma curve selected
    ILI9341_GMCTRP1, 15, 0x0F, 0x31, 0x2B, 0x0C, 0x0E, 0x08, // Set Gamma
    0x4E, 0xF1, 0x37, 0x07, 0x10, 0x03, 0x0E, 0x09, 0x00,
    ILI9341_GMCTRN1, 15, 0x00, 0x0E, 0x14, 0x03, 0x11, 0x07, // Set Gamma
    0x31, 0xC1, 0x48, 0x08, 0x0F, 0x0C, 0x31, 0x36, 0x0F,
    ILI9341_SLPOUT, 0x80, // Exit Sleep
    ILI9341_DISPON, 0x80, // Display on
    0x00                  // End of list
};

//*************************** User Functions ***************************//

void tft_begin(void);

void drawPixel(uint16_t x, uint16_t y, uint16_t color);
void drawHLine(uint16_t x, uint16_t y, uint16_t w, uint16_t color);
void drawVLine(uint16_t x, uint16_t y, uint16_t h, uint16_t color);
void fillRect(uint16_t x, uint16_t y, uint16_t w, uint16_t h, uint16_t color);
void fillScreen(uint16_t color);
void setRotation(uint8_t m);
void invertDisplay(bool i);
void pushColor(uint16_t color);
void tft_scrollTo(uint16_t y);

//************************* Non User Functions *************************//
void startWrite(void);
void endWrite(void);
void writeCommand(uint8_t cmd);
void setAddrWindow(uint16_t x1, uint16_t y1, uint16_t w, uint16_t h);
uint8_t tft_readcommand8(uint8_t reg, uint8_t index = 0);

/**************************************************************************/
/*!
    @brief  Call before issuing command(s) or data to display. Performs
            chip-select (if required). Required
            for all display types; not an SPI-specific function.
*/
/**************************************************************************/
void startWrite(void)
{
    output_low(TFT_CS);
}

/**************************************************************************/
/*!
    @brief  Call after issuing command(s) or data to display. Performs
            chip-deselect (if required). Required
            for all display types; not an SPI-specific function.
*/
/**************************************************************************/
void endWrite(void)
{
    output_high(TFT_CS);
}

/**************************************************************************/
/*!
    @brief  Write a single command byte to the display. Chip-select and
            transaction must have been previously set -- this ONLY sets
            the device to COMMAND mode, issues the byte and then restores
            DATA mode. There is no corresponding explicit writeData()
            function -- just use ILI9341_SPI_XFER().
    @param  cmd  8-bit command to write.
*/
/**************************************************************************/
void writeCommand(uint8_t cmd)
{
    output_low(TFT_DC);
    ILI9341_SPI_XFER(cmd);
    output_high(TFT_DC);
}

/**************************************************************************/
/*!
    @brief   Initialize ILI9341 chip
    Connects to the ILI9341 over SPI and sends initialization procedure commands
    @param    freq  Desired SPI clock frequency
*/
/**************************************************************************/
void tft_begin(void)
{

#ifdef TFT_RST
    output_high(TFT_RST);
    output_drive(TFT_RST);
    delay_ms(100);
    output_low(TFT_RST);
    delay_ms(100);
    output_high(TFT_RST);
    delay_ms(200);
#else // If no hardware reset pin...
    writeCommand(ILI9341_SWRESET); // Engage software reset
    delay_ms(150);
#endif
    output_high(TFT_CS);
    output_drive(TFT_CS);
    output_drive(TFT_DC);

    startWrite();

    uint8_t cmd, x, numArgs;
    rom uint8_t *addr = initcmd;
    cmd = *addr++;
    while (cmd > 0)
    {
        writeCommand(cmd);
        x = *addr++;
        numArgs = x & 0x7F;
        while (numArgs--)
            ILI9341_SPI_XFER(*addr++);
        if (x & 0x80)
            delay_ms(150);
        cmd = *addr++;
    }

    endWrite();

    _width = ILI9341_TFTWIDTH;
    _height = ILI9341_TFTHEIGHT;
    rotation = 0;
}

/**************************************************************************/
/*!
    @brief   Set the "address window" - the rectangle we will write to RAM with the next chunk of SPI data writes. The ILI9341 will automatically wrap the data as each row is filled
    @param   x1  TFT memory 'x' origin
    @param   y1  TFT memory 'y' origin
    @param   w   Width of rectangle
    @param   h   Height of rectangle
*/
/**************************************************************************/
void setAddrWindow(uint16_t x1, uint16_t y1, uint16_t w, uint16_t h)
{
    uint16_t x2 = (x1 + w - 1),
             y2 = (y1 + h - 1);
    writeCommand(ILI9341_CASET); // Column address set
    ILI9341_SPI_XFER(x1 >> 8);
    ILI9341_SPI_XFER(x1);
    ILI9341_SPI_XFER(x2 >> 8);
    ILI9341_SPI_XFER(x2);
    writeCommand(ILI9341_PASET); // Row address set
    ILI9341_SPI_XFER(y1 >> 8);
    ILI9341_SPI_XFER(y1);
    ILI9341_SPI_XFER(y2 >> 8);
    ILI9341_SPI_XFER(y2);
    writeCommand(ILI9341_RAMWR); // Write to RAM
}

/**************************************************************************/
/*!
    @brief  Set origin of (0,0) and orientation of TFT display
    @param  m  The index for rotation, from 0-3 inclusive
*/
/**************************************************************************/
void setRotation(uint8_t m)
{
    rotation = m % 4; // can't be higher than 3
    switch (rotation)
    {
    case 0:
        m = (MADCTL_MX | MADCTL_BGR);
        _width = ILI9341_TFTWIDTH;
        _height = ILI9341_TFTHEIGHT;
        break;
    case 1:
        m = (MADCTL_MV | MADCTL_BGR);
        _width = ILI9341_TFTHEIGHT;
        _height = ILI9341_TFTWIDTH;
        break;
    case 2:
        m = (MADCTL_MY | MADCTL_BGR);
        _width = ILI9341_TFTWIDTH;
        _height = ILI9341_TFTHEIGHT;
        break;
    case 3:
        m = (MADCTL_MX | MADCTL_MY | MADCTL_MV | MADCTL_BGR);
        _width = ILI9341_TFTHEIGHT;
        _height = ILI9341_TFTWIDTH;
        break;
    }

    startWrite();
    writeCommand(ILI9341_MADCTL);
    ILI9341_SPI_XFER(m);
    endWrite();
}

void drawPixel(uint16_t x, uint16_t y, uint16_t color)
{
    if ((x < _width) && (y < _height))
    {
        startWrite();
        setAddrWindow(x, y, 1, 1);
        ILI9341_SPI_XFER(color >> 8);
        ILI9341_SPI_XFER(color & 0xFF);
        endWrite();
    }
}

/**************************************************************************/
/*!
   @brief    Draw a perfectly horizontal line (this is often optimized in a subclass!)
    @param    x   Left-most x coordinate
    @param    y   Left-most y coordinate
    @param    w   Width in pixels
   @param    color 16-bit 5-6-5 Color to fill with
*/
/**************************************************************************/
void drawHLine(uint16_t x, uint16_t y, uint16_t w, uint16_t color)
{
    if ((x < _width) && (y < _height) && w)
    {
        uint8_t hi = color >> 8, lo = color;

        if ((x + w - 1) >= _width)
            w = _width - x;
        startWrite();
        setAddrWindow(x, y, w, 1);
        while (w--)
        {
            ILI9341_SPI_XFER(hi);
            ILI9341_SPI_XFER(lo);
        }
        endWrite();
    }
}

/**************************************************************************/
/*!
   @brief    Draw a perfectly vertical line (this is often optimized in a subclass!)
    @param    x   Top-most x coordinate
    @param    y   Top-most y coordinate
    @param    h   Height in pixels
   @param    color 16-bit 5-6-5 Color to fill with
*/
/**************************************************************************/
void drawVLine(uint16_t x, uint16_t y, uint16_t h, uint16_t color)
{
    if ((x < _width) && (y < _height) && h)
    {
        uint8_t hi = color >> 8, lo = color;
        if ((y + h - 1) >= _height)
            h = _height - y;
        startWrite();
        setAddrWindow(x, y, 1, h);
        while (h--)
        {
            ILI9341_SPI_XFER(hi);
            ILI9341_SPI_XFER(lo);
        }
        endWrite();
    }
}

/**************************************************************************/
/*!
   @brief    Fill a rectangle completely with one color. Update in subclasses if desired!
    @param    x   Top left corner x coordinate
    @param    y   Top left corner y coordinate
    @param    w   Width in pixels
    @param    h   Height in pixels
   @param    color 16-bit 5-6-5 Color to fill with
*/
/**************************************************************************/
void fillRect(uint16_t x, uint16_t y, uint16_t w, uint16_t h, uint16_t color)
{
    if (w && h)
    { // Nonzero width and height?
        uint8_t hi = color >> 8, lo = color;
        if ((x >= _width) || (y >= _height))
            return;
        if ((x + w - 1) >= _width)
            w = _width - x;
        if ((y + h - 1) >= _height)
            h = _height - y;
        startWrite();
        setAddrWindow(x, y, w, h);
        uint32_t px = (uint32_t)w * h;
        while (px--)
        {
            ILI9341_SPI_XFER(hi);
            ILI9341_SPI_XFER(lo);
        }
        endWrite();
    }
}

/**************************************************************************/
/*!
   @brief    Fill the screen completely with one color. Update in subclasses if desired!
    @param    color 16-bit 5-6-5 Color to fill with
*/
/**************************************************************************/
void fillScreen(uint16_t color)
{
    fillRect(0, 0, _width, _height, color);
}

/**************************************************************************/
/*!
    @brief  Invert the colors of the display (if supported by hardware).
            Self-contained, no transaction setup required.
    @param  i  true = inverted display, false = normal display.
*/
/**************************************************************************/
void invertDisplay(bool i)
{
    startWrite();
    writeCommand(i ? ILI9341_INVON : ILI9341_INVOFF);
    endWrite();
}

/**************************************************************************/
/*!
    @brief   Scroll display memory
    @param   y How many pixels to scroll display by
*/
/**************************************************************************/
void tft_scrollTo(uint16_t y)
{
    startWrite();
    writeCommand(ILI9341_VSCRSADD);
    ILI9341_SPI_XFER(y >> 8);
    ILI9341_SPI_XFER(y);
    endWrite();
}

/**************************************************************************/
/*!
   @brief  Read 8 bits of data from ILI9341 configuration memory. NOT from RAM!
           This is highly undocumented/supported, it's really a hack but kinda works?
    @param    command  The command register to read data from
    @param    index  The byte index into the command to read from
    @return   Unsigned 8-bit data read from ILI9341 register
*/
/**************************************************************************/
uint8_t tft_readcommand8(uint8_t command, uint8_t index)
{
    startWrite();
    writeCommand(0xD9); // woo sekret command?
    ILI9341_SPI_XFER(0x10 + index);
    writeCommand(command);
    uint8_t r = ILI9341_SPI_XFER(0xFF);
    endWrite();
    return r;
}

/*!
    @brief  Essentially writePixel() with a transaction around it. I don't
            think this is in use by any of our code anymore (believe it was
            for some older BMP-reading examples), but is kept here in case
            any user code relies on it. Consider it DEPRECATED.
    @param  color  16-bit pixel color in '565' RGB format.
*/
void pushColor(uint16_t color)
{
    uint8_t hi = color >> 8, lo = color;
    startWrite();
    ILI9341_SPI_XFER(hi);
    ILI9341_SPI_XFER(lo);
    endWrite();
}

// end of code.
