RamiroMadera/Proyecto_GENERATOR/firmware_v3/Prueba_XPT/pruebaxpt.h

/*=============================================================================
 * Author: Ulises <->
 * Date: 2024/11/21
 * Version: 1
 *===========================================================================*/

/*=====[Avoid multiple inclusion - begin]====================================*/

#ifndef __PRUEBA_MPU_H__
#define __PRUEBA_MPU_H__

/*=====[Inclusions of public function dependencies]==========================*/

#include <stdint.h>
#include <stddef.h>
#include <ili9341_LPC4337_patch.h>

/*=====[C++ - begin]=========================================================*/

#ifdef __cplusplus
extern "C" {
#endif

/*=====[Definition macros of public constants]===============================*/

/*=====[Public function-like macros]=========================================*/

/*=====[Definitions of public data types]====================================*/

/*=====[Prototypes (declarations) of public functions]=======================*/

/*=====[Prototypes (declarations) of public interrupt functions]=============*/

/*=====[C++ - end]===========================================================*/

#ifdef __cplusplus
}
#endif

/*=====[Avoid multiple inclusion - end]======================================*/

#endif /* __PRUEBA_MPU_H__ */
